StonedEdge/Retro-Lite-CM5/enclosure/Solidworks/AX210 PCIe Card.SLDASM

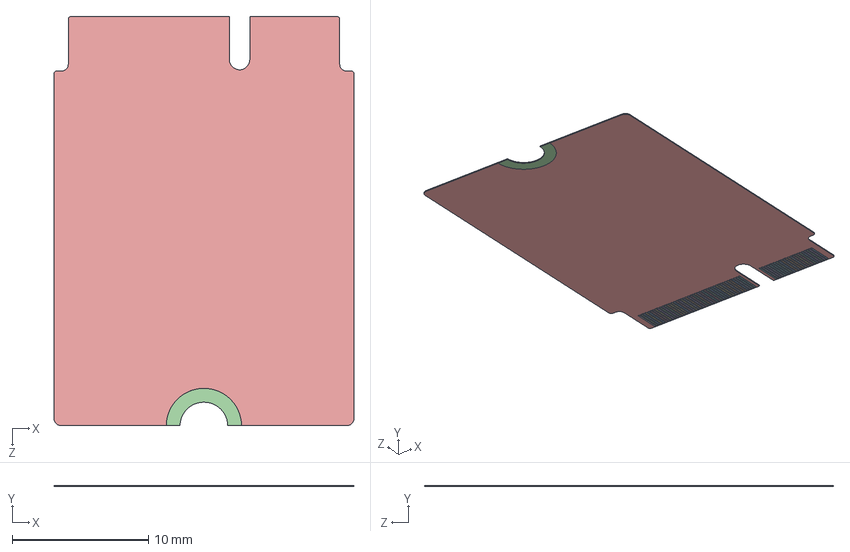
[picture p15: CAD file, 2024-07-26]
enclosure/Solidworks/AX210 PCIe Card.SLDASM
22.0 x 0.1 x 30.0 mm
AX210 PCIe Card-0
AX210 PCIe Card-1
AX210 PCIe Card-2
