StonedEdge/Retro-Lite-CM5/enclosure/Solidworks/Assembly Right PCB Controller.SLDASM

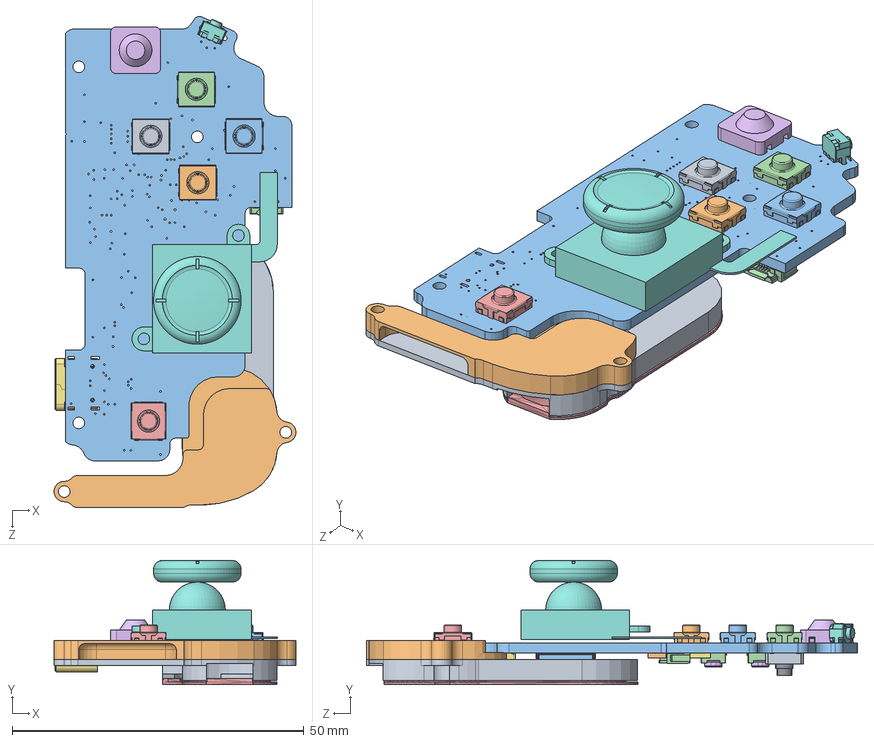
[picture p16: CAD file, 2024-07-26]
enclosure/Solidworks/Assembly Right PCB Controller.SLDASM
41.5 x 21.2 x 84.1 mm
Speaker Duct
Speaker Duct Lower
Board (39)
Frame x 2
Cover x 2
Stem x 2
Terminal x 8
Switch Joystick Blank
dualtact_BBStore v1
MPU-6050--3DModel-STEP-1 v1
5034801700 v1
505110-0592 v1
Printed-Speaker-Duct-Lid v1
Single Silicone Cap
RP2040_QFN_PACKAGE v1
436333033816 v1
Retro Lite CM5 (Latest)-11
Retro Lite CM5 (Latest)-12
Retro Lite CM5 (Latest)-13
Retro Lite CM5 (Latest)-14
Retro Lite CM5 (Latest)-15
Retro Lite CM5 (Latest)-16
Retro Lite CM5 (Latest)-17
