StonedEdge/Retro-Lite-CM5/enclosure/Solidworks/ZR Trigger_1.SLDPRT

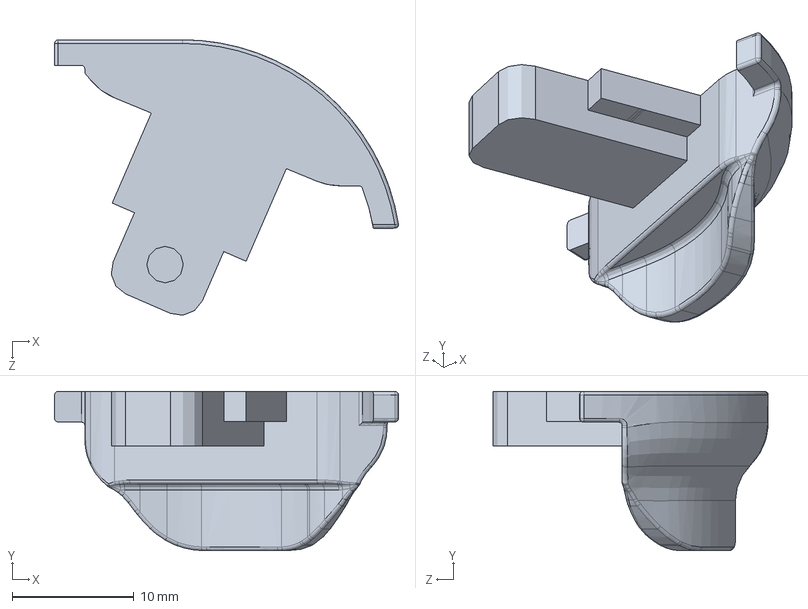
[picture p17: CAD file, 2024-07-26]
enclosure/Solidworks/ZR Trigger_1.SLDPRT
28.3 x 13.1 x 22.6 mm
