StonedEdge/Retro-Lite-CM5/enclosure/STL_V2/Case Front (OLED) - Fix outer surface face.stl

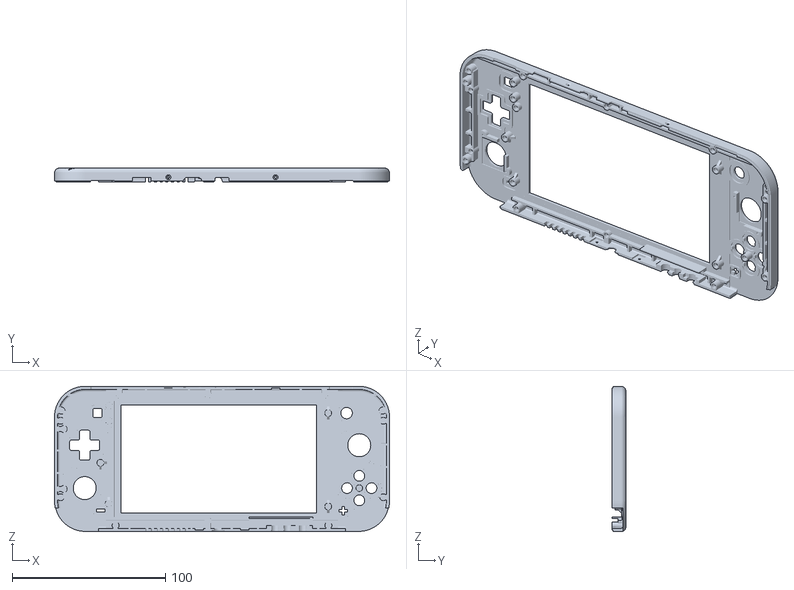
[picture p18: CAD file, 2025-11-29]
enclosure/STL_V2/Case Front (OLED) - Fix outer surface face.stl
218.8 x 9.00 x 95.0
