StonedEdge/Retro-Lite-CM5/enclosure/Solidworks/Start_Button_1.SLDPRT

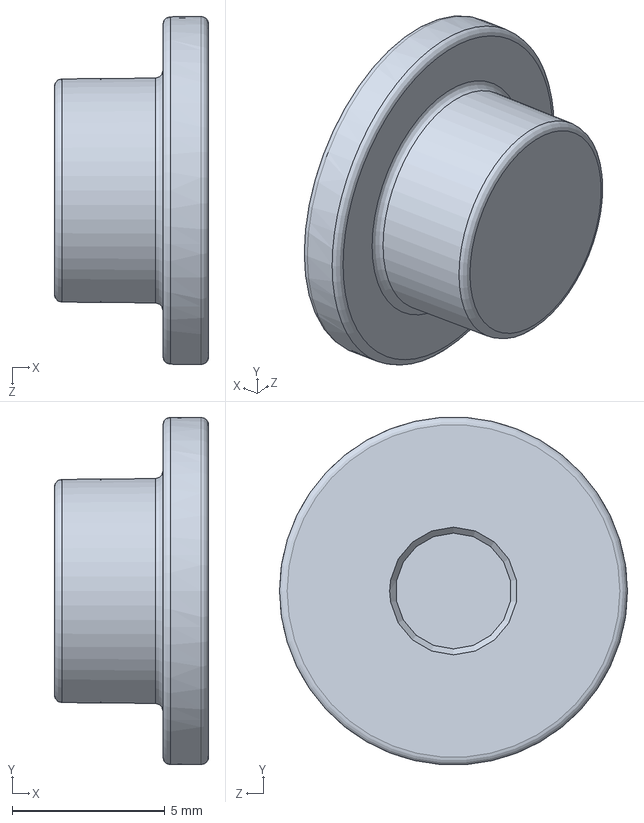
[picture p19: CAD file, 2024-07-26]
enclosure/Solidworks/Start_Button_1.SLDPRT
5.05 x 11.4 x 11.4 mm
