StonedEdge/Retro-Lite-CM5/enclosure/Solidworks/U9.SLDPRT

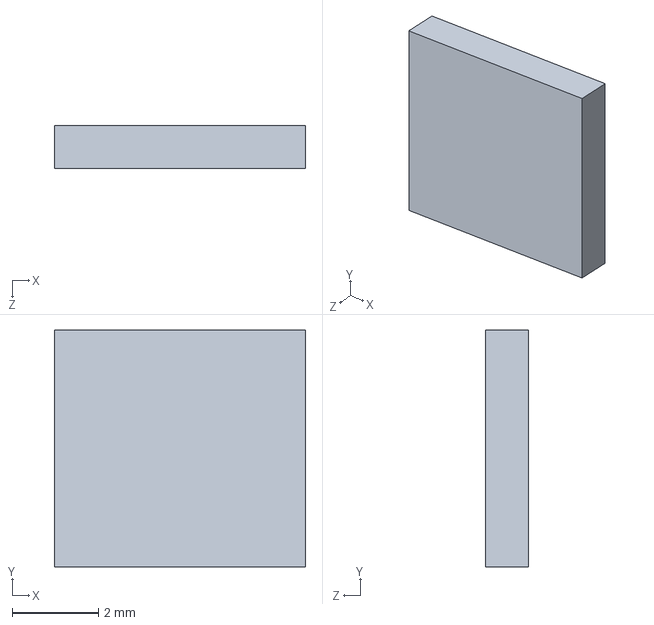
[picture p20: CAD file, 2024-07-26]
enclosure/Solidworks/U9.SLDPRT
5.84 x 5.50 x 1.00 mm
