StonedEdge/Retro-Lite-CM5/enclosure/Solidworks/Retro Lite CM5 (Latest)-18.SLDPRT

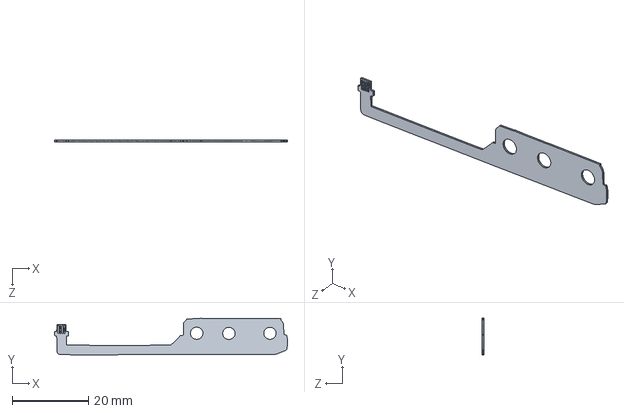
[picture p21: CAD file, 2024-07-26]
enclosure/Solidworks/Retro Lite CM5 (Latest)-18.SLDPRT
61.0 x 9.58 x 0.4 mm
