StonedEdge/Retro-Lite-CM5/enclosure/STL_V2/Button Spacers.stl

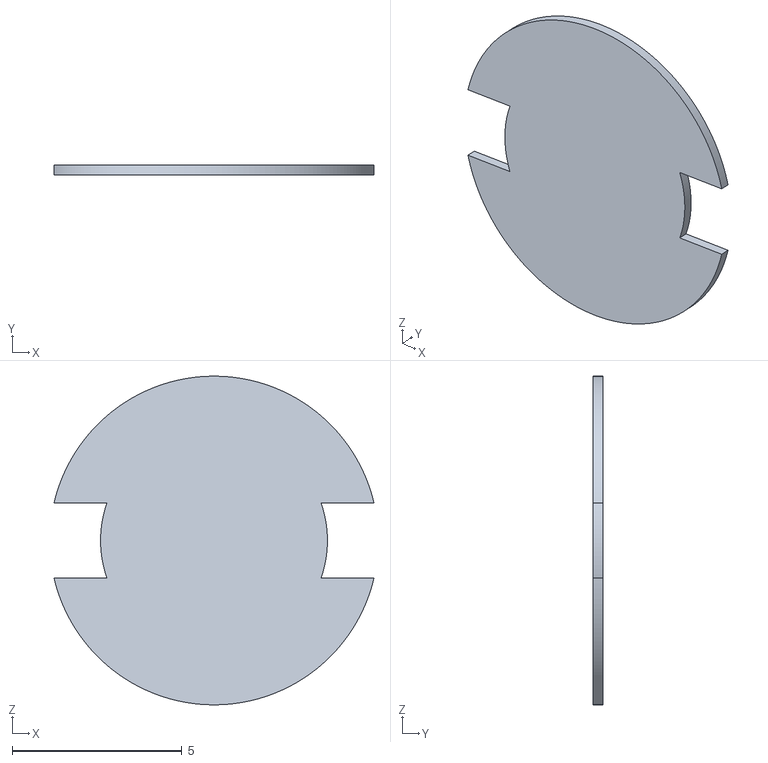
[picture p22: CAD file, 2025-06-07]
enclosure/STL_V2/Button Spacers.stl
9.43 x 0.3 x 9.69
