StonedEdge/Retro-Lite-CM5/enclosure/Solidworks/Retro Lite CM5 (Latest)-12.SLDPRT

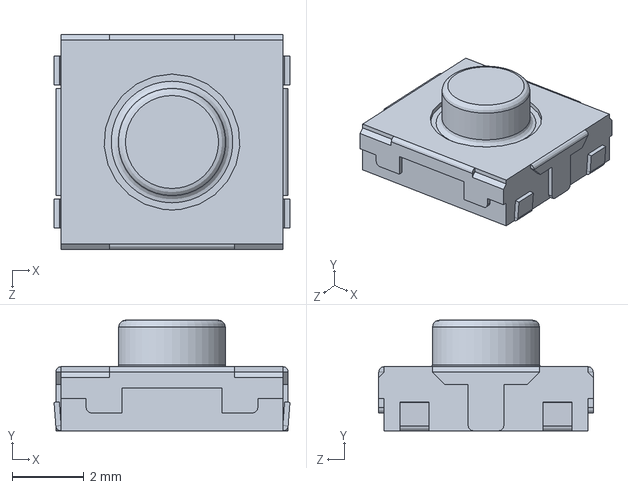
[picture p23: CAD file, 2024-07-26]
enclosure/Solidworks/Retro Lite CM5 (Latest)-12.SLDPRT
6.60 x 3.10 x 6.00 mm
