StonedEdge/Retro-Lite-CM5/enclosure/STL_V2/Button Rotation Stopper Bracket.stl

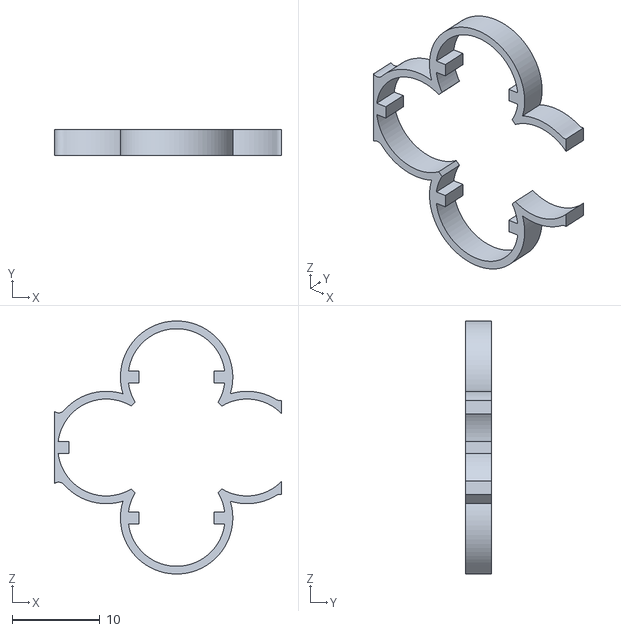
[picture p24: CAD file, 2025-06-07]
enclosure/STL_V2/Button Rotation Stopper Bracket.stl
25.9 x 3.00 x 28.8
