StonedEdge/Retro-Lite-CM5/enclosure/STL_V2/Battery Bracket (5000mAh).stl

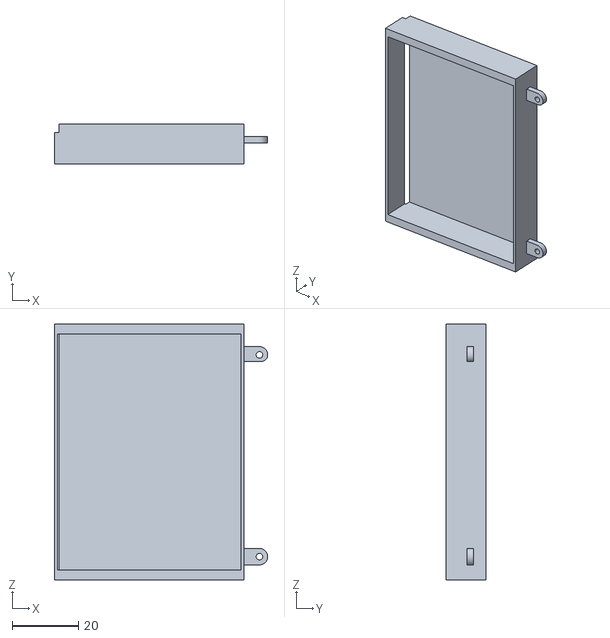
[picture p25: CAD file, 2025-06-03]
enclosure/STL_V2/Battery Bracket (5000mAh).stl
64.5 x 12.0 x 77.4
