StonedEdge/Retro-Lite-CM5/enclosure/Solidworks/Speaker Duct Lower.SLDPRT

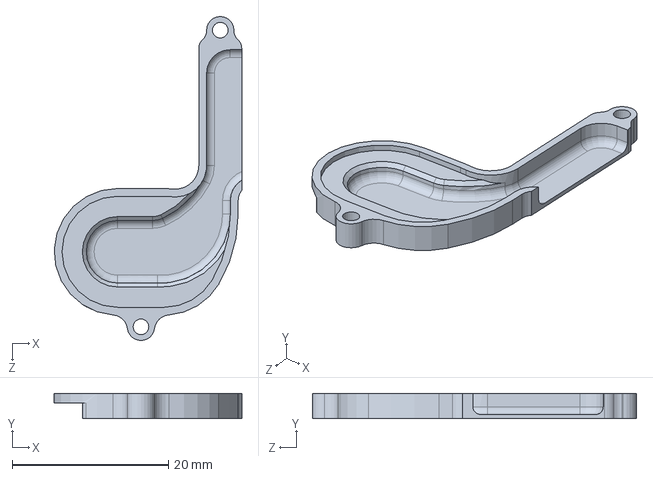
[picture p26: CAD file, 2024-07-26]
enclosure/Solidworks/Speaker Duct Lower.SLDPRT
24.0 x 3.20 x 41.5 mm
