StonedEdge/Retro-Lite-CM5/enclosure/STL_V2/Case Rear (Smaller Vent Holes).stl

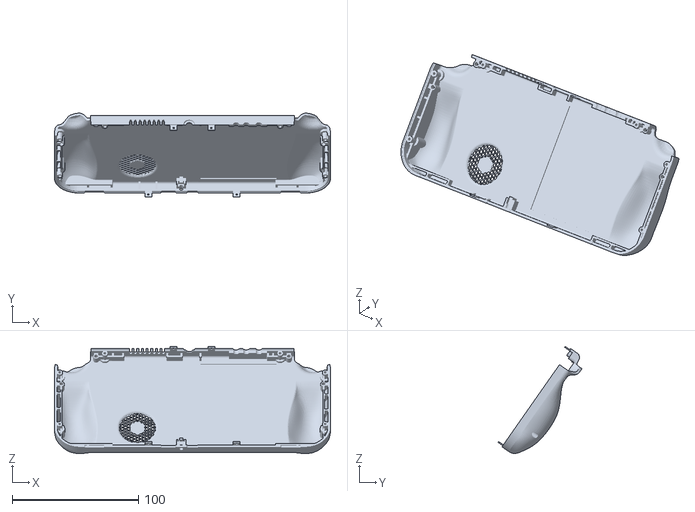
[picture p27: CAD file, 2024-12-22]
enclosure/STL_V2/Case Rear (Smaller Vent Holes).stl
219.0 x 66.5 x 84.9
