StonedEdge/Retro-Lite-CM5/enclosure/Solidworks/Terminal.SLDPRT

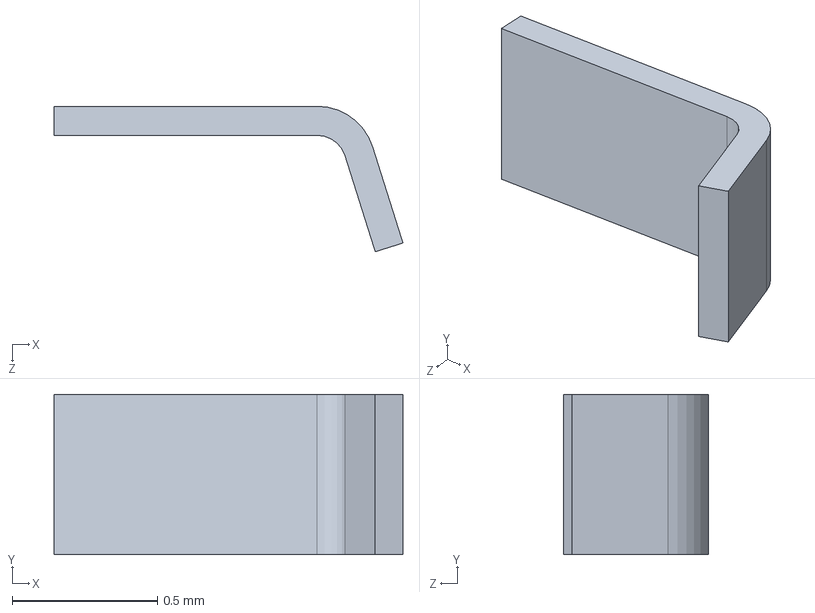
[picture p28: CAD file, 2024-07-26]
enclosure/Solidworks/Terminal.SLDPRT
1.20 x 0.55 x 0.5 mm
