StonedEdge/Retro-Lite-CM5/enclosure/STL_V2/Case Front (OLED).stl

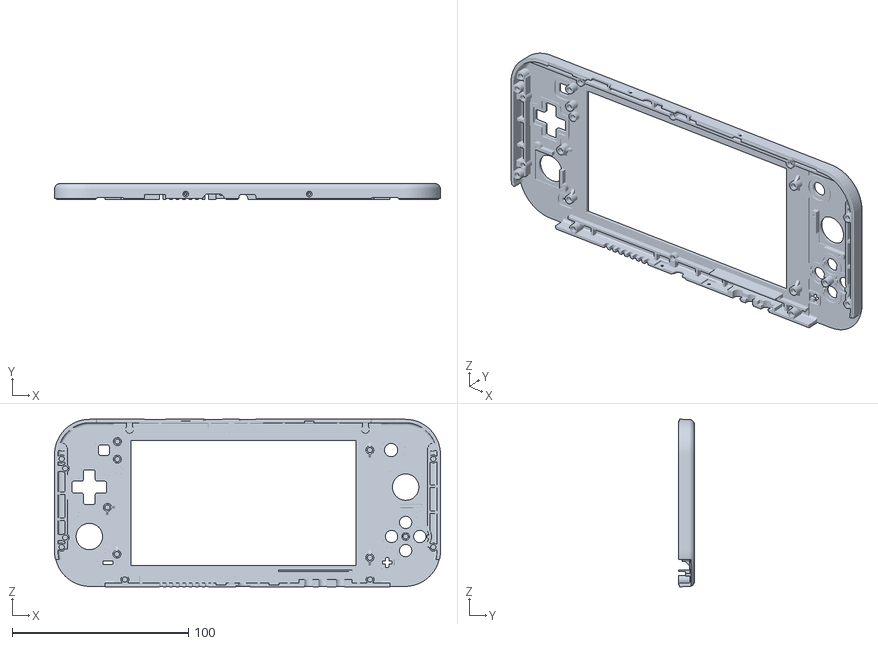
[picture p29: CAD file, 2024-09-26]
enclosure/STL_V2/Case Front (OLED).stl
218.8 x 9.00 x 95.0
