StonedEdge/Retro-Lite-CM5/enclosure/STL_V2/Battery Bracket (8000mAh).stl

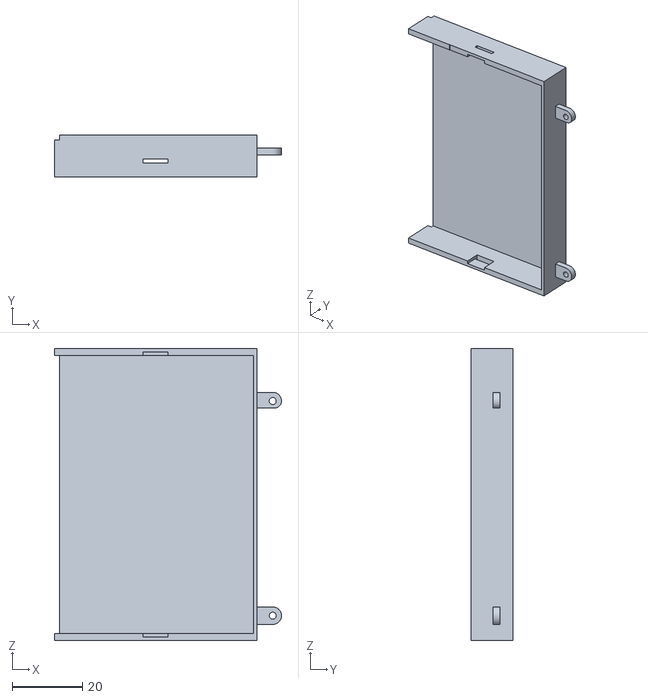
[picture p30: CAD file, 2024-07-11]
enclosure/STL_V2/Battery Bracket (8000mAh).stl
64.5 x 12.0 x 83.0
