StonedEdge/Retro-Lite-CM5/enclosure/Solidworks/Switch Joystick Blank.SLDPRT

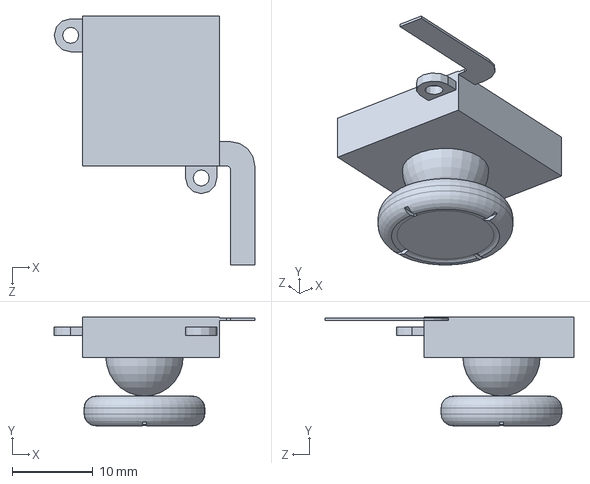
[picture p31: CAD file, 2024-07-26]
enclosure/Solidworks/Switch Joystick Blank.SLDPRT
24.9 x 13.5 x 30.9 mm
