StonedEdge/Retro-Lite-CM5/enclosure/STL_V2/Trigger_Spacer.stl

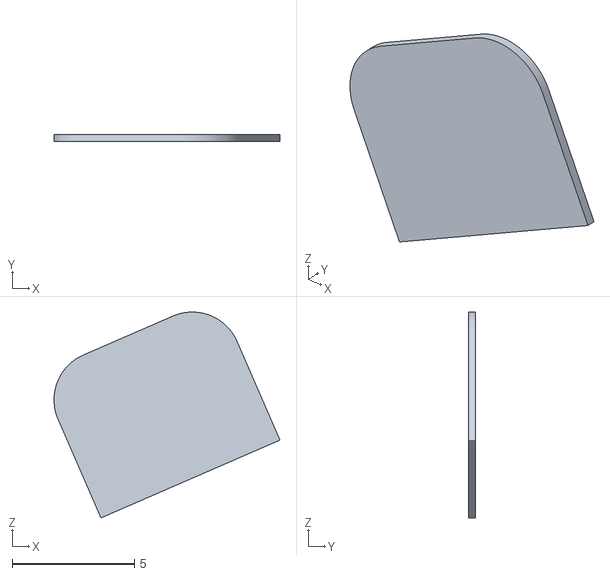
[picture p32: CAD file, 2024-07-11]
enclosure/STL_V2/Trigger_Spacer.stl
9.26 x 0.3 x 8.44
