StonedEdge/Retro-Lite-CM5/enclosure/Solidworks/Speaker Duct.SLDPRT

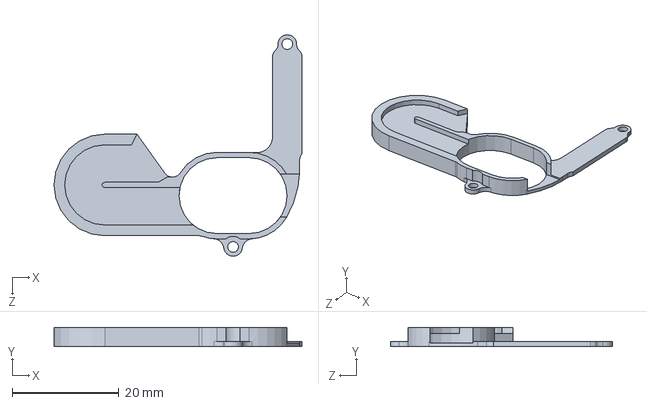
[picture p33: CAD file, 2024-07-26]
enclosure/Solidworks/Speaker Duct.SLDPRT
46.4 x 3.60 x 41.5 mm
