StonedEdge/Retro-Lite-CM5/enclosure/STL_V2/Power Button.stl

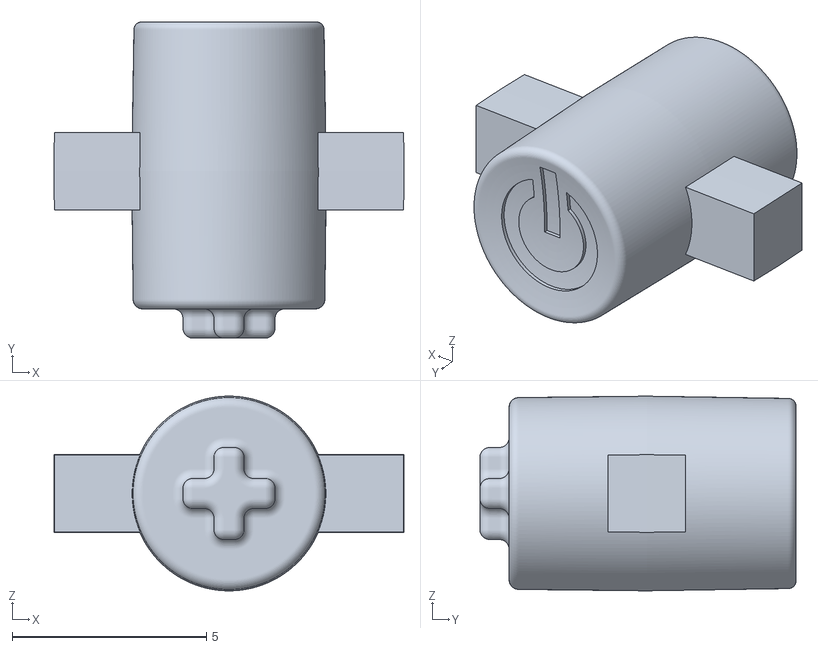
[picture p34: CAD file, 2024-06-27]
enclosure/STL_V2/Power Button.stl
9.02 x 8.15 x 5.02
