StonedEdge/Retro-Lite-CM5/enclosure/Solidworks/VLCF4020T-220MR56--3DModel-STEP-56544 v1.SLDPRT

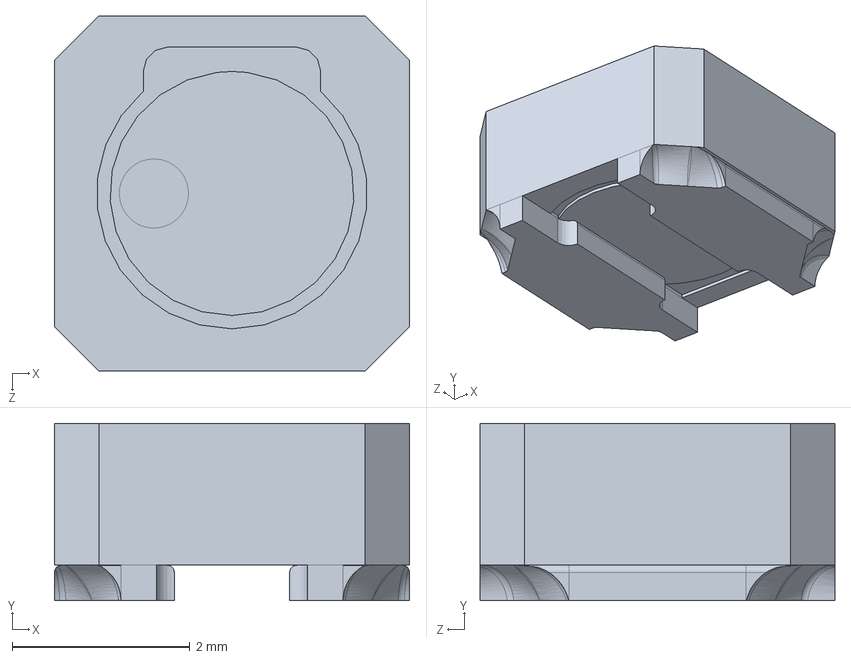
[picture p35: CAD file, 2024-07-26]
enclosure/Solidworks/VLCF4020T-220MR56--3DModel-STEP-56544 v1.SLDPRT
4.00 x 2.00 x 4.00 mm
