StonedEdge/Retro-Lite-CM5/enclosure/STL_V2/Case Rear.stl

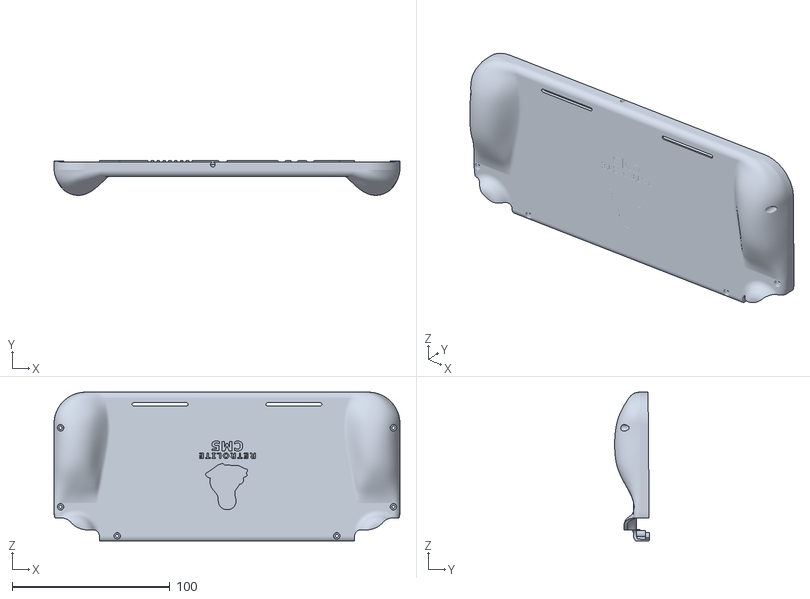
[picture p36: CAD file, 2024-06-27]
enclosure/STL_V2/Case Rear.stl
219.0 x 22.0 x 94.1
