StonedEdge/Retro-Lite-CM5/enclosure/Solidworks/NuckDeck B_1.SLDPRT

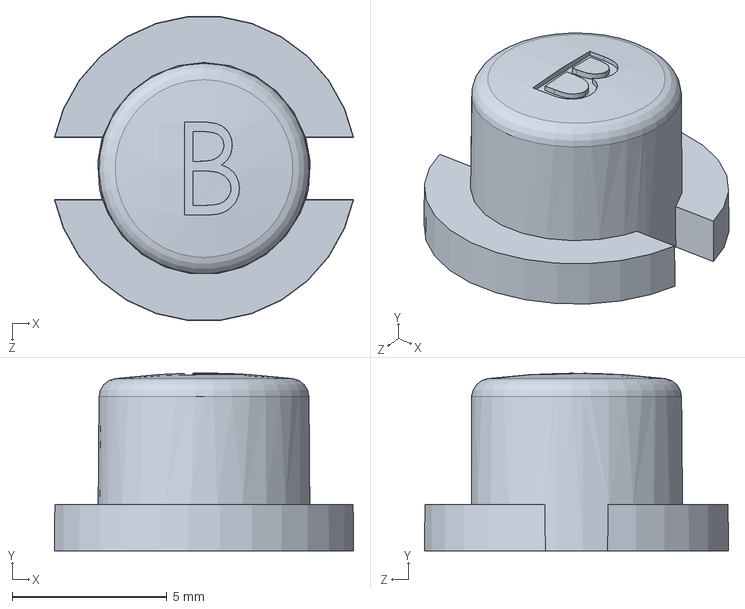
[picture p37: CAD file, 2024-07-26]
enclosure/Solidworks/NuckDeck B_1.SLDPRT
9.68 x 5.75 x 9.83 mm
