StonedEdge/Retro-Lite-CM5/enclosure/STL_V2/Volume Buttons.stl

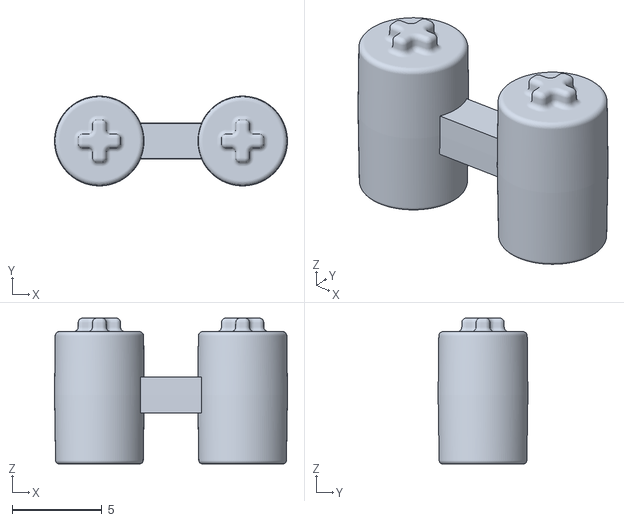
[picture p38: CAD file, 2024-06-27]
enclosure/STL_V2/Volume Buttons.stl
13.0 x 5.02 x 8.15
