StonedEdge/Retro-Lite-CM5/enclosure/STL_V2/Case Front.stl

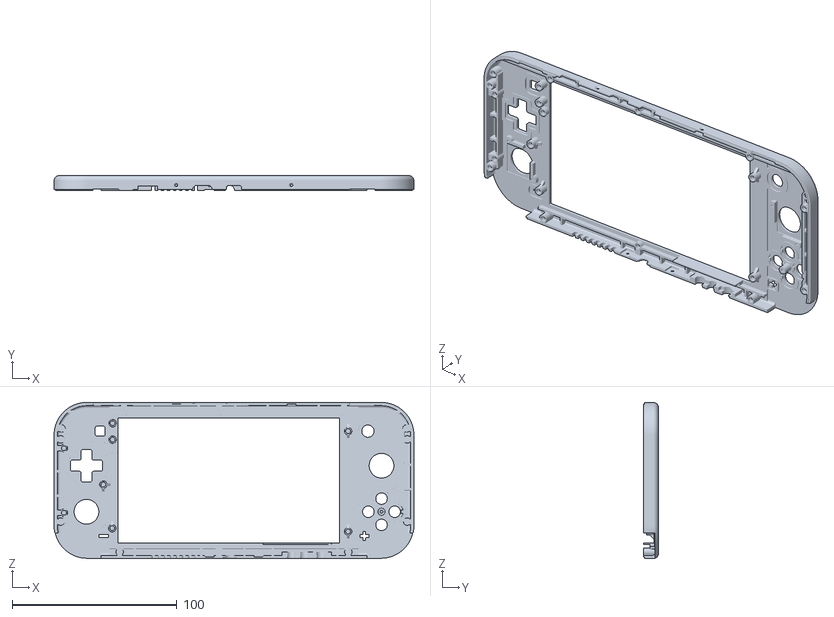
[picture p39: CAD file, 2024-06-27]
enclosure/STL_V2/Case Front.stl
218.8 x 9.00 x 95.0
