StonedEdge/Retro-Lite-CM5/enclosure/Solidworks/TSIC 306 SOP-8--3DModel-STEP-510211 v1.SLDPRT

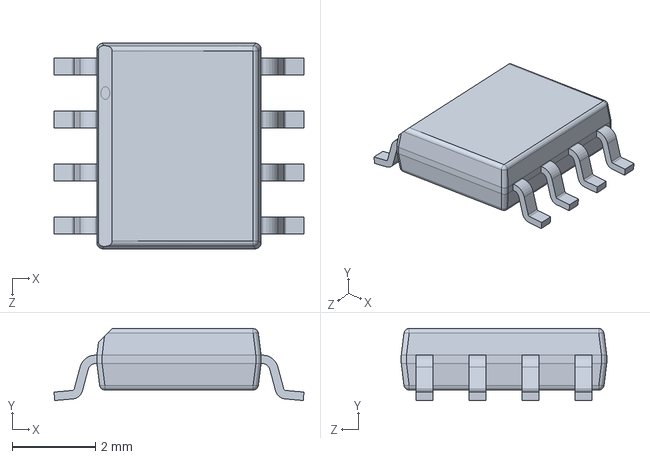
[picture p40: CAD file, 2024-07-26]
enclosure/Solidworks/TSIC 306 SOP-8--3DModel-STEP-510211 v1.SLDPRT
5.99 x 1.73 x 4.93 mm
