StonedEdge/Retro-Lite-CM5/enclosure/STL_V2/Fan Bracket.stl

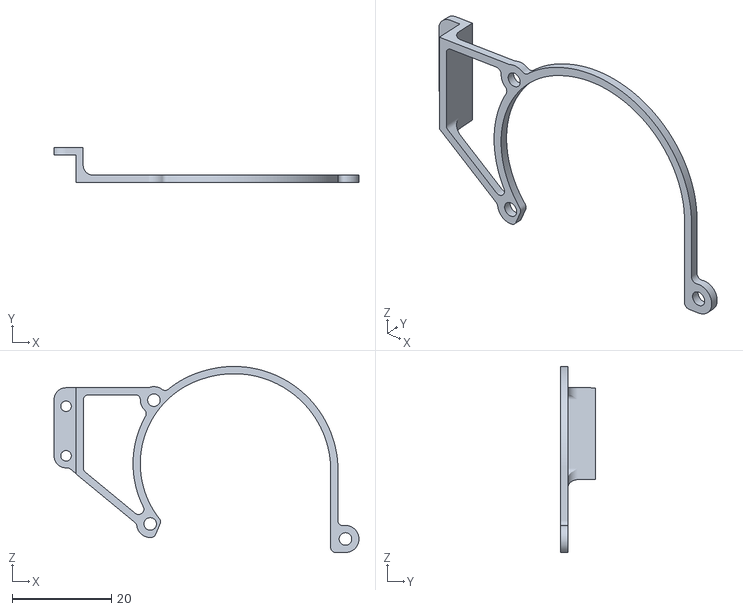
[picture p41: CAD file, 2024-06-27]
enclosure/STL_V2/Fan Bracket.stl
61.5 x 7.08 x 37.5
