StonedEdge/Retro-Lite-CM5/enclosure/Solidworks/refine_Cut001.SLDPRT

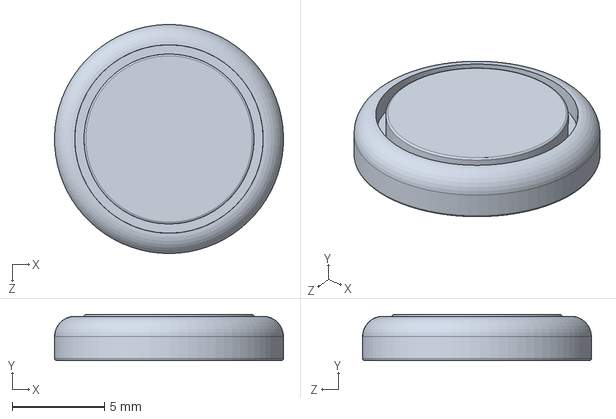
[picture p42: CAD file, 2024-07-26]
enclosure/Solidworks/refine_Cut001.SLDPRT
12.4 x 2.50 x 12.4 mm
