StonedEdge/Retro-Lite-CM5/enclosure/STL_V2/Rear Trigger Bracket .stl

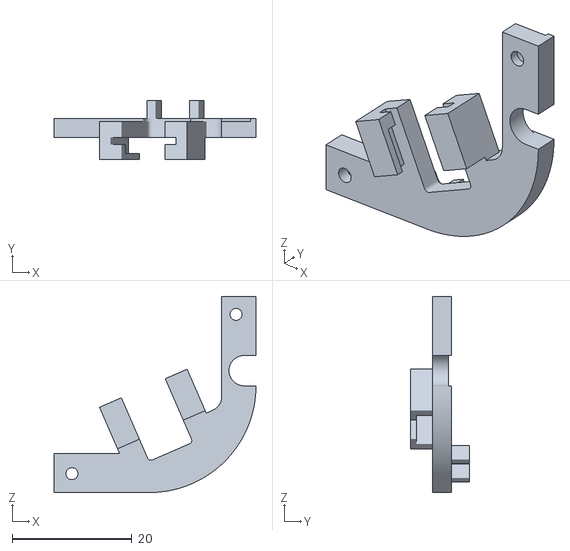
[picture p43: CAD file, 2024-06-08]
enclosure/STL_V2/Rear Trigger Bracket .stl
33.8 x 9.90 x 32.8
