StonedEdge/Retro-Lite-CM5/enclosure/Solidworks/U4302.SLDPRT

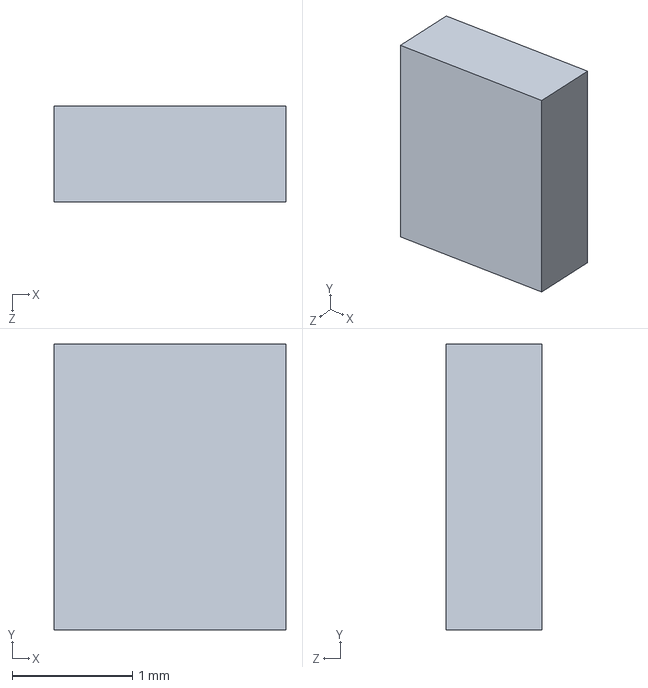
[picture p44: CAD file, 2024-07-26]
enclosure/Solidworks/U4302.SLDPRT
1.93 x 2.38 x 0.8 mm
