StonedEdge/Retro-Lite-CM5/enclosure/Solidworks/Silicone Button Cap_DPAD.SLDPRT

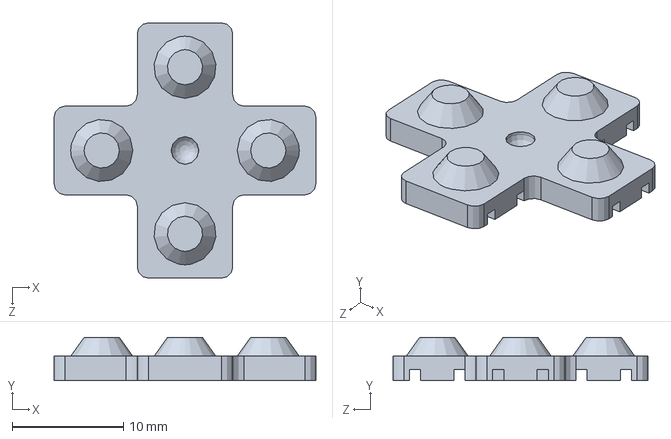
[picture p45: CAD file, 2024-07-26]
enclosure/Solidworks/Silicone Button Cap_DPAD.SLDPRT
23.6 x 3.90 x 23.0 mm
