StonedEdge/Retro-Lite-CM5/enclosure/STL_V2/Silicone_Membrane_Mold_Lower.stl

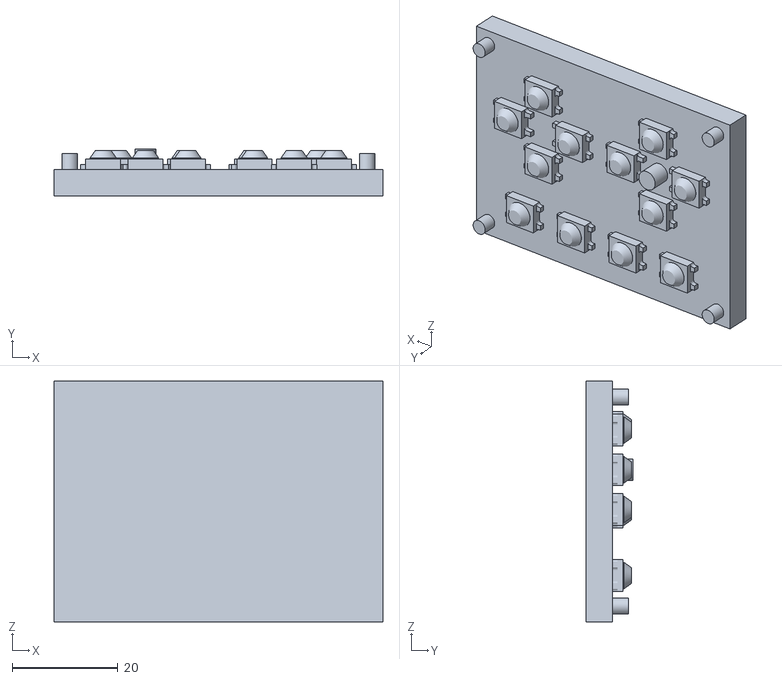
[picture p46: CAD file, 2024-04-26]
enclosure/STL_V2/Silicone_Membrane_Mold_Lower.stl
62.2 x 8.90 x 45.5
