StonedEdge/Retro-Lite-CM5/enclosure/Solidworks/refine_Revolution001.SLDPRT

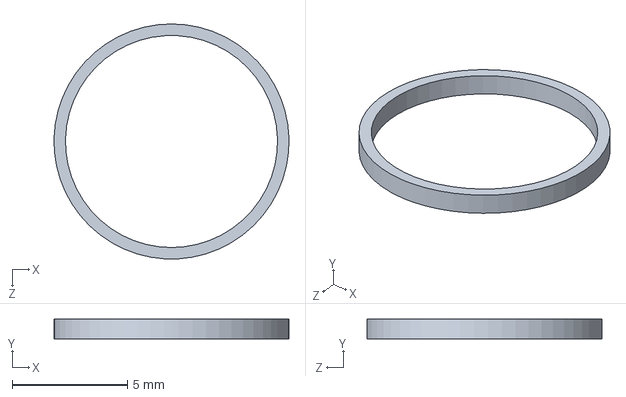
[picture p47: CAD file, 2024-07-26]
enclosure/Solidworks/refine_Revolution001.SLDPRT
10.2 x 0.85 x 10.2 mm
