StonedEdge/Retro-Lite-CM5/enclosure/STL_V2/Silicone_Membrane_Mold_Upper.stl

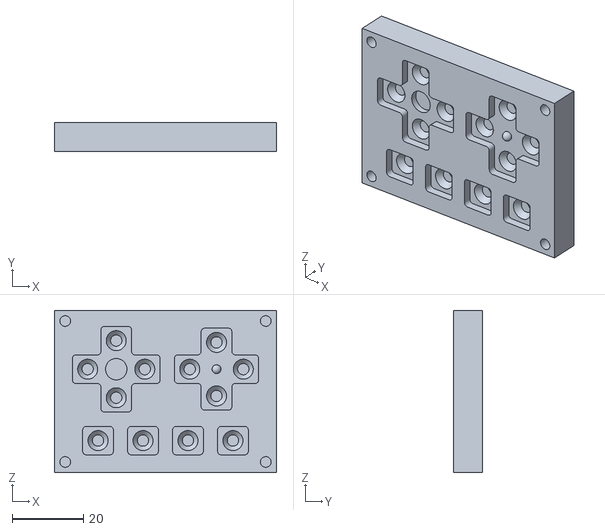
[picture p48: CAD file, 2024-04-26]
enclosure/STL_V2/Silicone_Membrane_Mold_Upper.stl
62.2 x 8.00 x 45.5
