StonedEdge/Retro-Lite-CM5/enclosure/Solidworks/Switch Lite Fan_1.SLDPRT

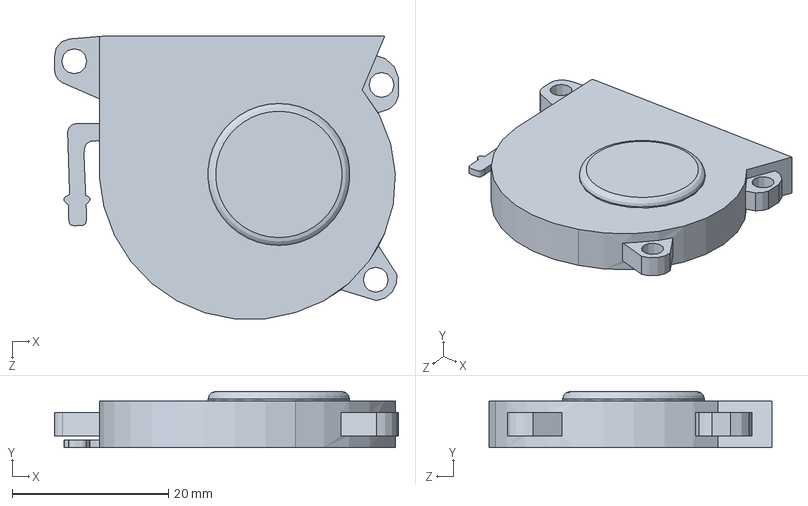
[picture p49: CAD file, 2024-07-26]
enclosure/Solidworks/Switch Lite Fan_1.SLDPRT
44.1 x 7.20 x 36.3 mm
