StonedEdge/Retro-Lite-CM5/enclosure/Solidworks/Y1.SLDPRT

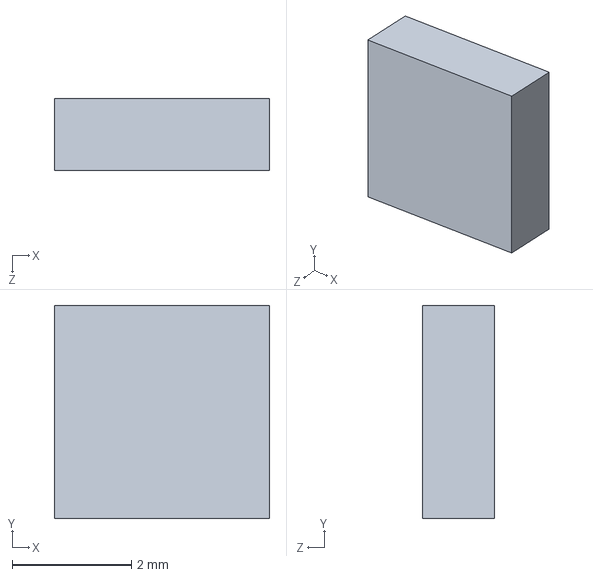
[picture p50: CAD file, 2024-07-26]
enclosure/Solidworks/Y1.SLDPRT
3.60 x 3.57 x 1.20 mm
