StonedEdge/Retro-Lite-CM5/enclosure/Solidworks/U8.SLDPRT

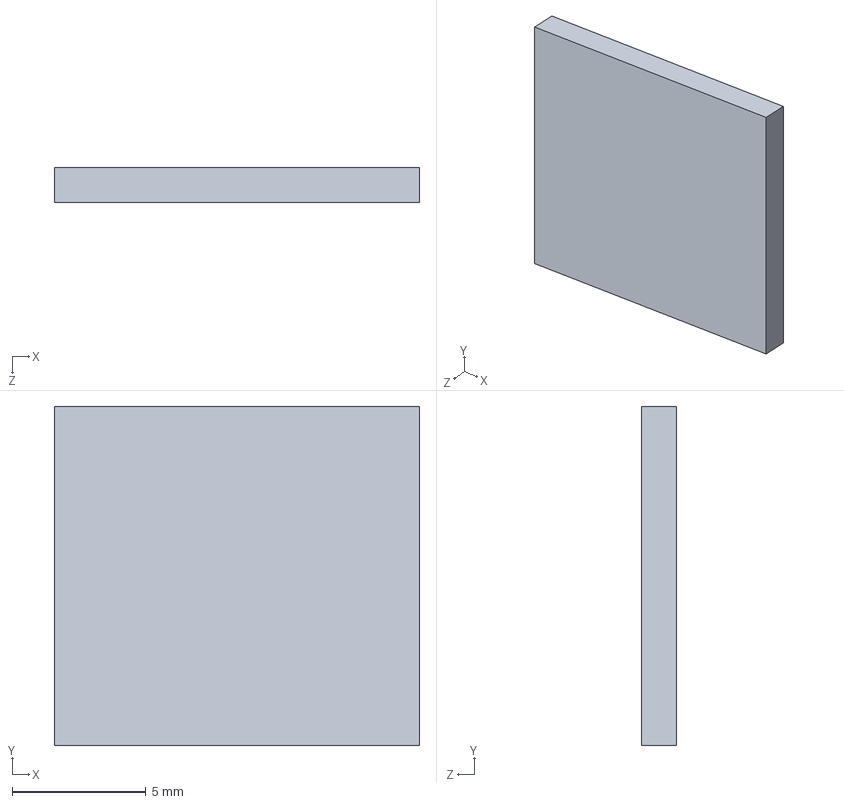
[picture p51: CAD file, 2024-07-26]
enclosure/Solidworks/U8.SLDPRT
13.7 x 12.7 x 1.30 mm
