StonedEdge/Retro-Lite-CM5/enclosure/Solidworks/U4301.SLDPRT

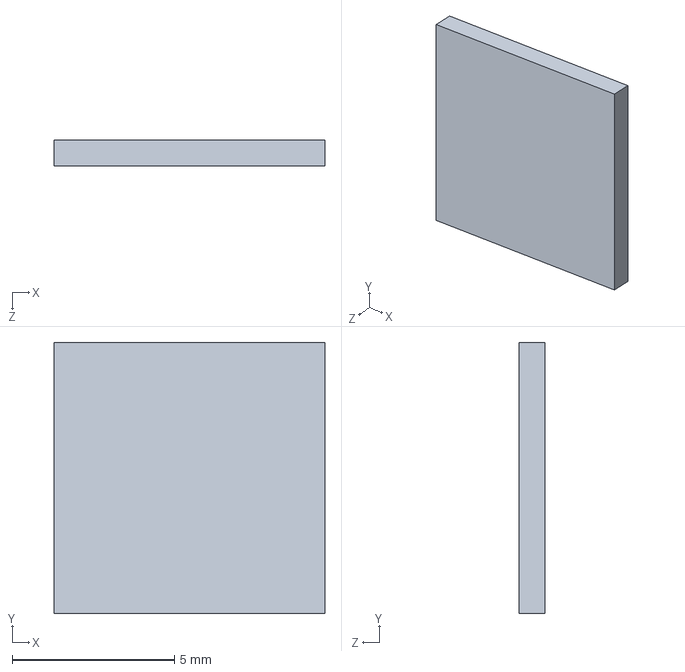
[picture p52: CAD file, 2024-07-26]
enclosure/Solidworks/U4301.SLDPRT
8.35 x 8.35 x 0.8 mm
