StonedEdge/Retro-Lite-CM5/enclosure/STL_V2/Right Speaker Cover.stl

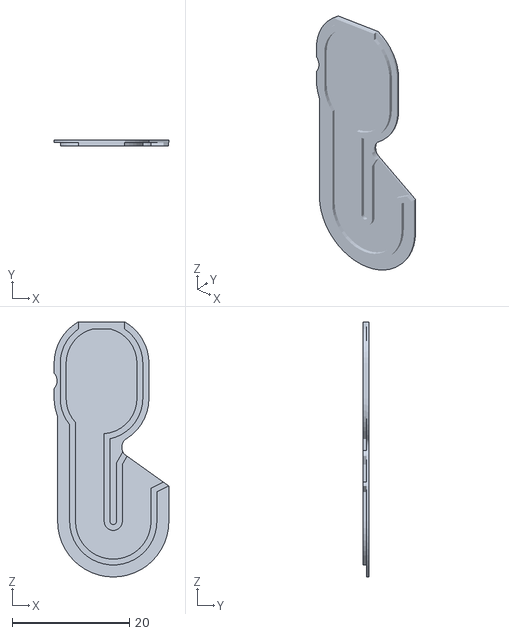
[picture p53: CAD file, 2024-03-31]
enclosure/STL_V2/Right Speaker Cover.stl
19.6 x 1.00 x 43.5
