StonedEdge/Retro-Lite-CM5/enclosure/Solidworks/R24.SLDPRT

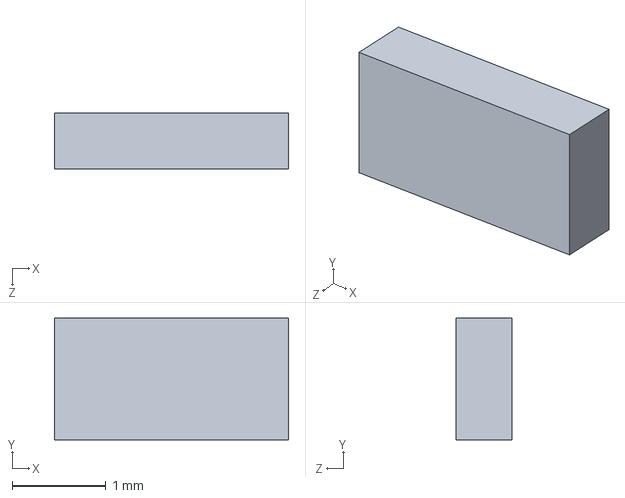
[picture p54: CAD file, 2024-07-26]
enclosure/Solidworks/R24.SLDPRT
2.50 x 1.30 x 0.6 mm
