StonedEdge/Retro-Lite-CM5/enclosure/Solidworks/Silicone Button Cap_Circle.SLDPRT

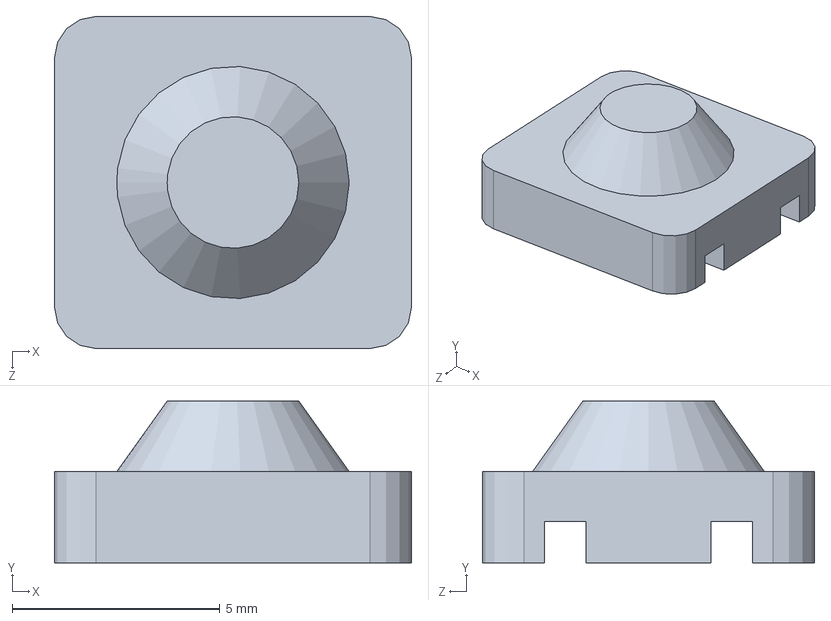
[picture p55: CAD file, 2024-07-26]
enclosure/Solidworks/Silicone Button Cap_Circle.SLDPRT
8.60 x 3.90 x 8.00 mm
