StonedEdge/Retro-Lite-CM5/enclosure/Solidworks/Q4.SLDPRT

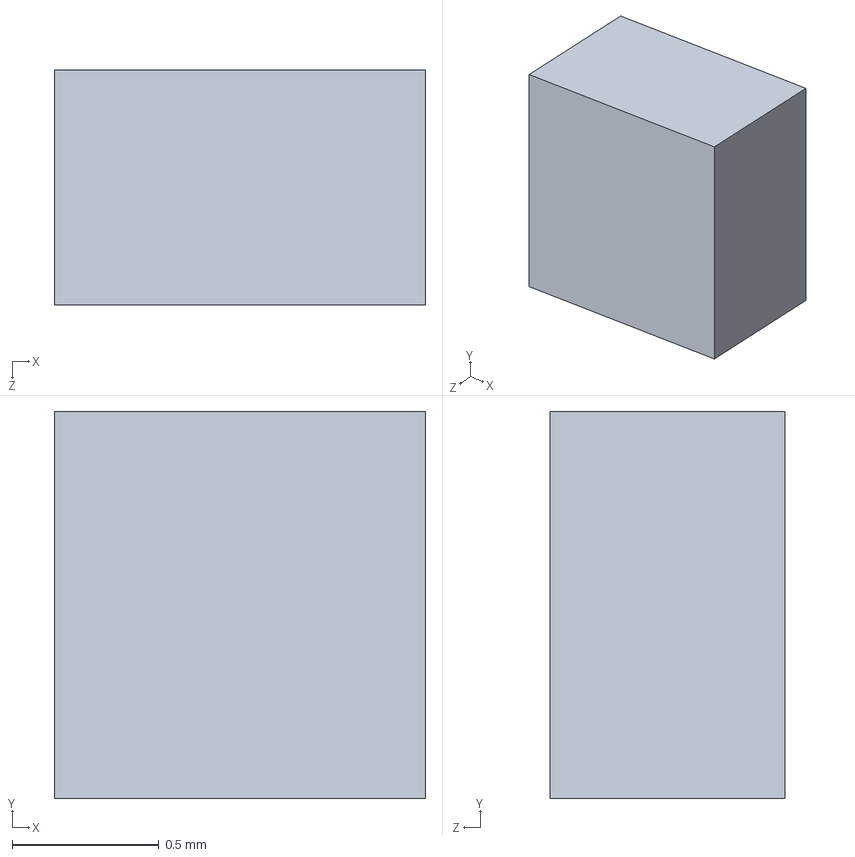
[picture p56: CAD file, 2024-07-26]
enclosure/Solidworks/Q4.SLDPRT
1.27 x 1.32 x 0.8 mm
