StonedEdge/Retro-Lite-CM5/enclosure/STL_V2/Plus Hotkey.stl

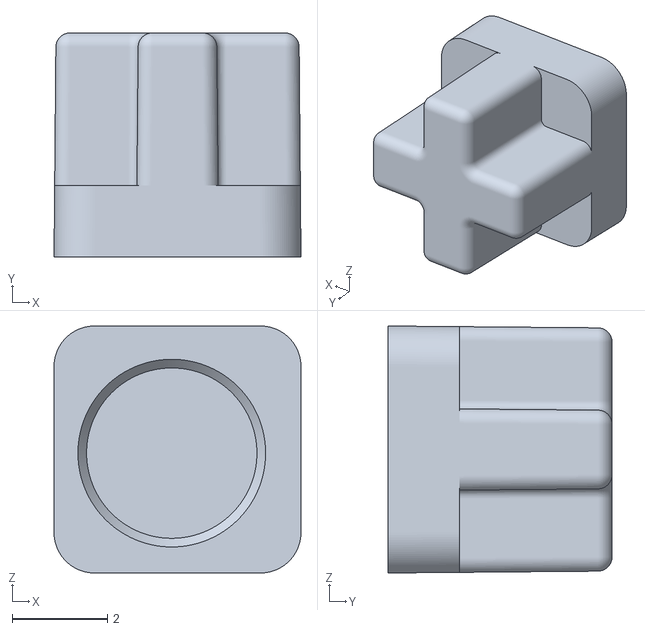
[picture p57: CAD file, 2024-03-04]
enclosure/STL_V2/Plus Hotkey.stl
5.18 x 4.70 x 5.18
