StonedEdge/Retro-Lite-CM5/enclosure/STL_V2/Trigger.stl

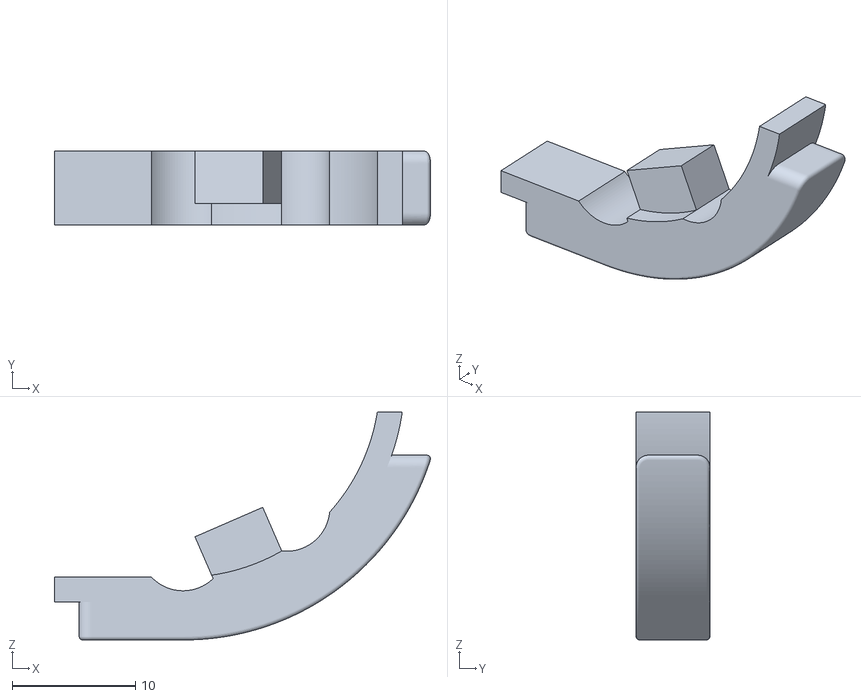
[picture p58: CAD file, 2024-02-13]
enclosure/STL_V2/Trigger.stl
30.5 x 6.00 x 18.5
