StonedEdge/Retro-Lite-CM5/enclosure/Solidworks/Stem.SLDPRT

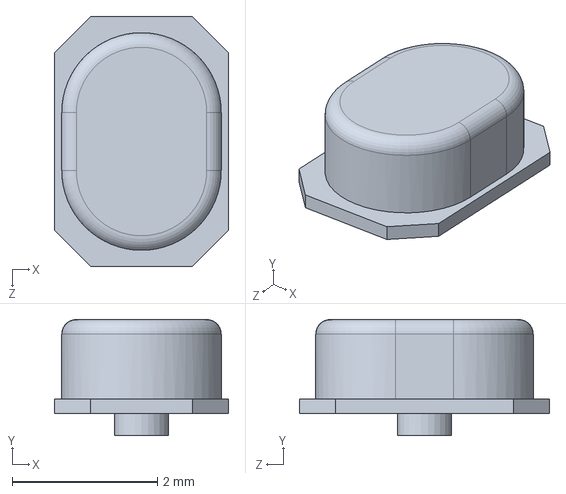
[picture p59: CAD file, 2024-07-26]
enclosure/Solidworks/Stem.SLDPRT
2.40 x 1.60 x 3.45 mm
