StonedEdge/Retro-Lite-CM5/enclosure/Solidworks/Silicone Button Cap_ABXY.SLDPRT

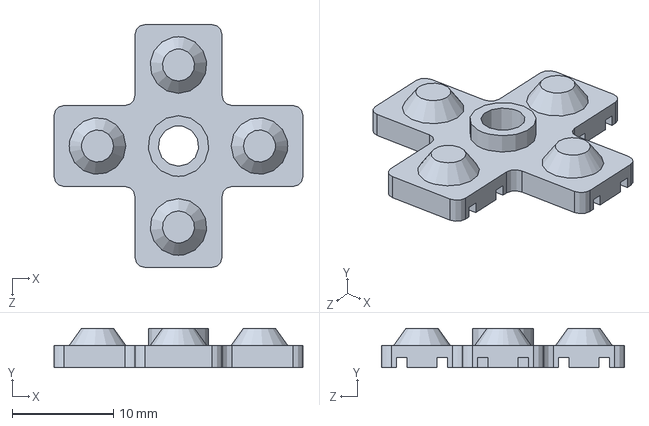
[picture p60: CAD file, 2024-07-26]
enclosure/Solidworks/Silicone Button Cap_ABXY.SLDPRT
24.6 x 3.90 x 24.0 mm
