StonedEdge/Retro-Lite-CM5/enclosure/STL_V2/B.stl

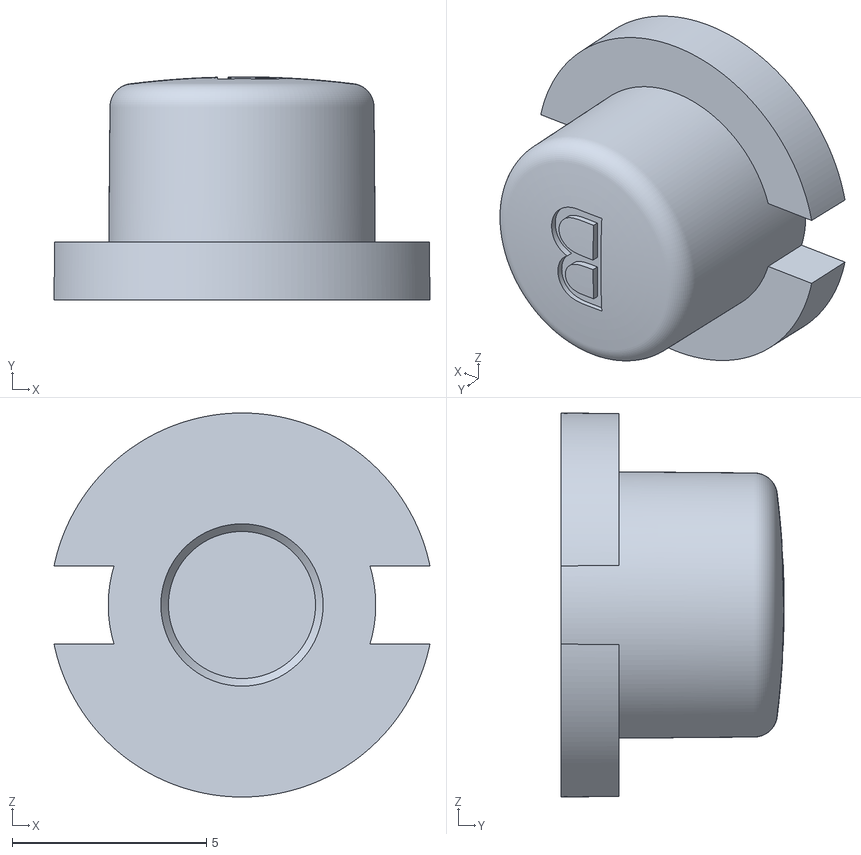
[picture p61: CAD file, 2024-02-08]
enclosure/STL_V2/B.stl
9.68 x 5.75 x 9.89
