StonedEdge/Retro-Lite-CM5/enclosure/STL_V2/Start.stl

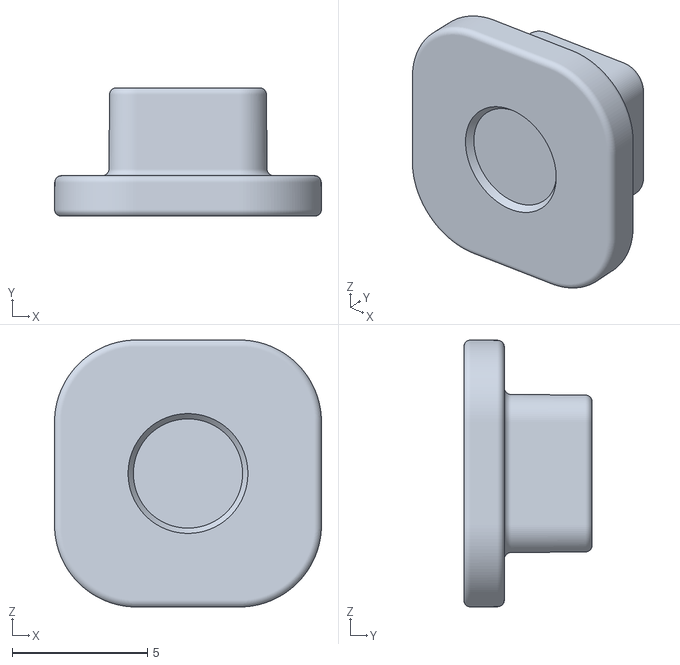
[picture p62: CAD file, 2024-02-08]
enclosure/STL_V2/Start.stl
9.88 x 4.75 x 9.88
