StonedEdge/Retro-Lite-CM5/enclosure/Solidworks/Retro Lite CM5 (Latest)-17.SLDPRT

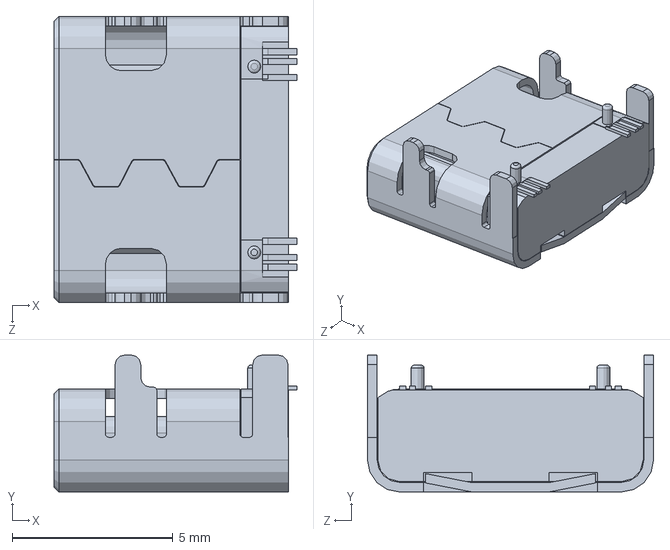
[picture p63: CAD file, 2024-07-26]
enclosure/Solidworks/Retro Lite CM5 (Latest)-17.SLDPRT
7.56 x 4.26 x 8.90 mm
