StonedEdge/Retro-Lite-CM5/enclosure/STL_V2/DPAD.stl

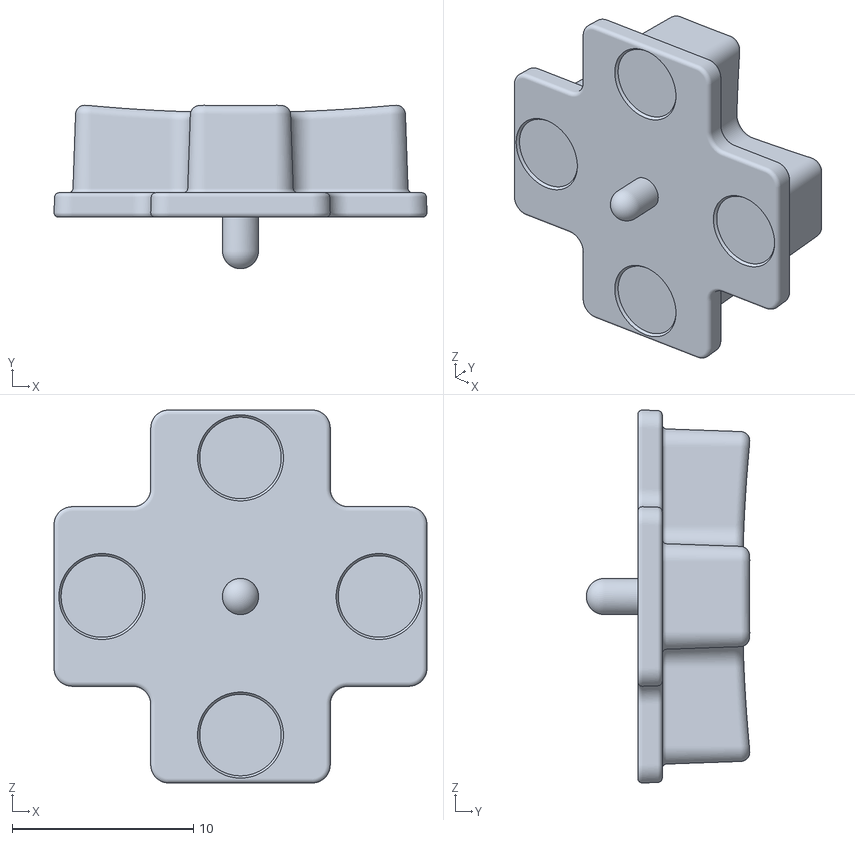
[picture p64: CAD file, 2024-02-08]
enclosure/STL_V2/DPAD.stl
20.6 x 9.03 x 20.6
