StonedEdge/Retro-Lite-CM5/enclosure/STL_V2/Minus Hotkey.stl

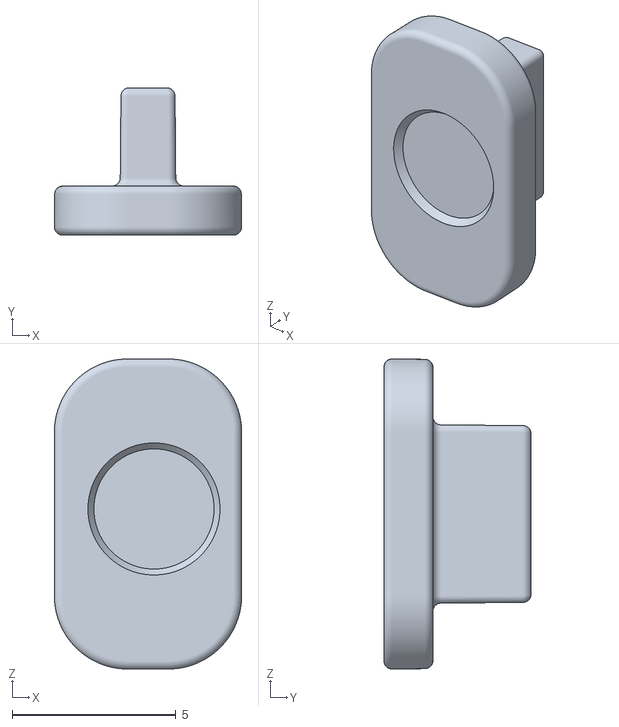
[picture p65: CAD file, 2024-02-08]
enclosure/STL_V2/Minus Hotkey.stl
5.72 x 4.50 x 9.47
