StonedEdge/Retro-Lite-CM5/enclosure/Solidworks/R1.SLDPRT

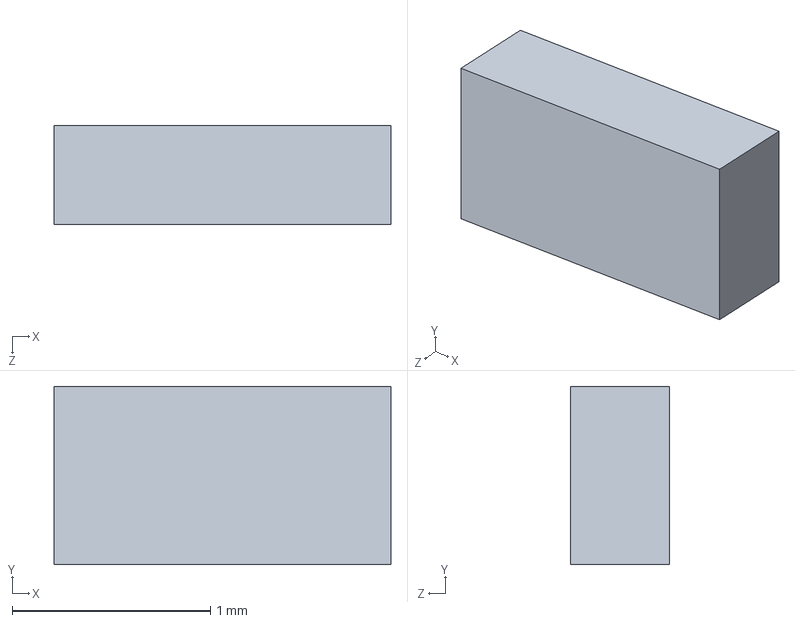
[picture p66: CAD file, 2024-07-26]
enclosure/Solidworks/R1.SLDPRT
1.70 x 0.9 x 0.5 mm
