StonedEdge/Retro-Lite-CM5/enclosure/Solidworks/U5.SLDPRT

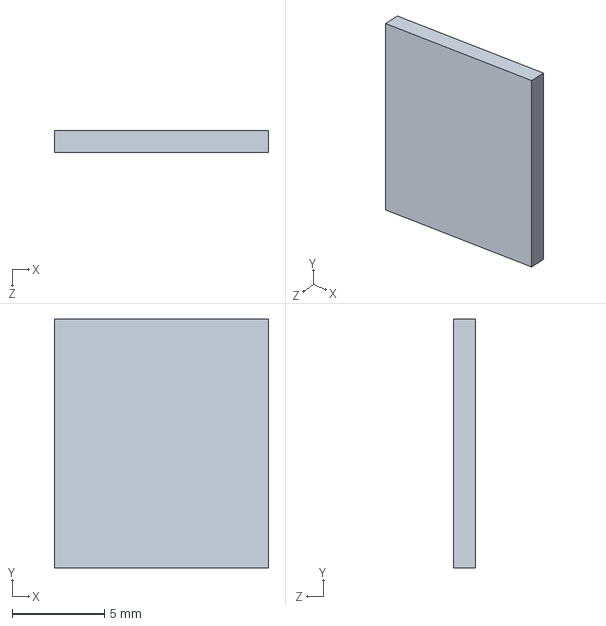
[picture p67: CAD file, 2024-07-26]
enclosure/Solidworks/U5.SLDPRT
11.6 x 13.5 x 1.20 mm
