StonedEdge/Retro-Lite-CM5/enclosure/Solidworks/Pin1.SLDPRT

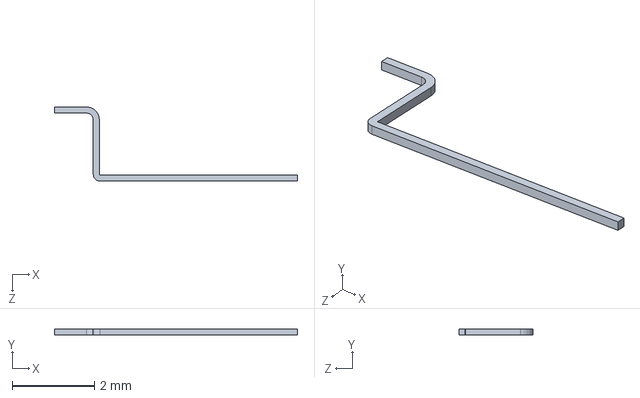
[picture p68: CAD file, 2024-07-26]
enclosure/Solidworks/Pin1.SLDPRT
5.90 x 0.15 x 1.80 mm
