StonedEdge/Retro-Lite-CM5/enclosure/Solidworks/U1.SLDPRT

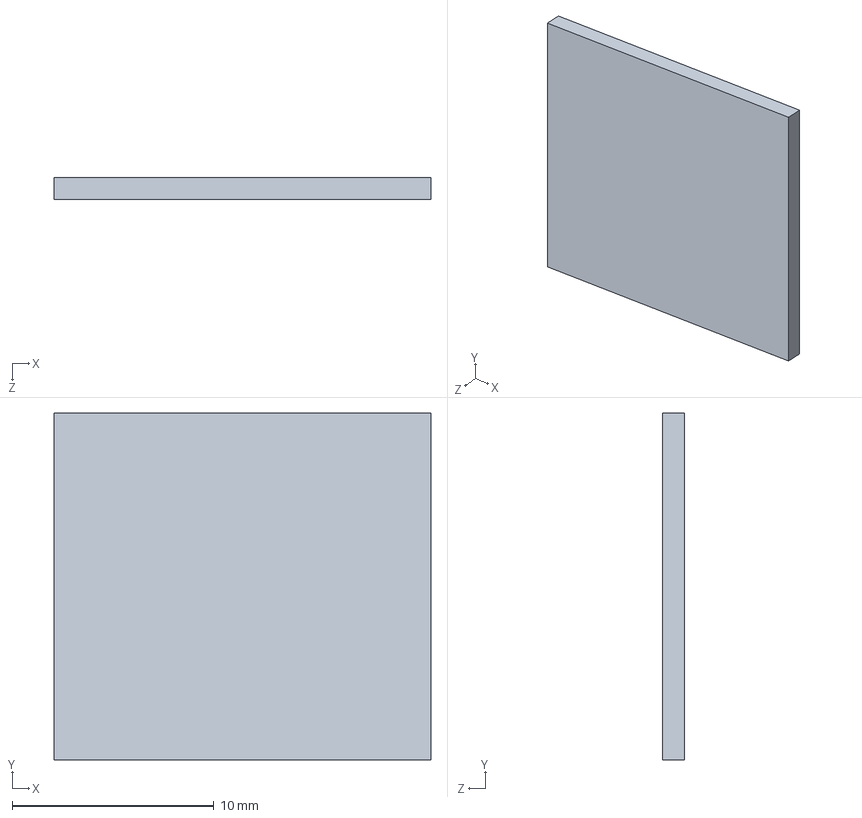
[picture p69: CAD file, 2024-07-26]
enclosure/Solidworks/U1.SLDPRT
18.7 x 17.2 x 1.10 mm
