StonedEdge/Retro-Lite-CM5/enclosure/Solidworks/Q5.SLDPRT

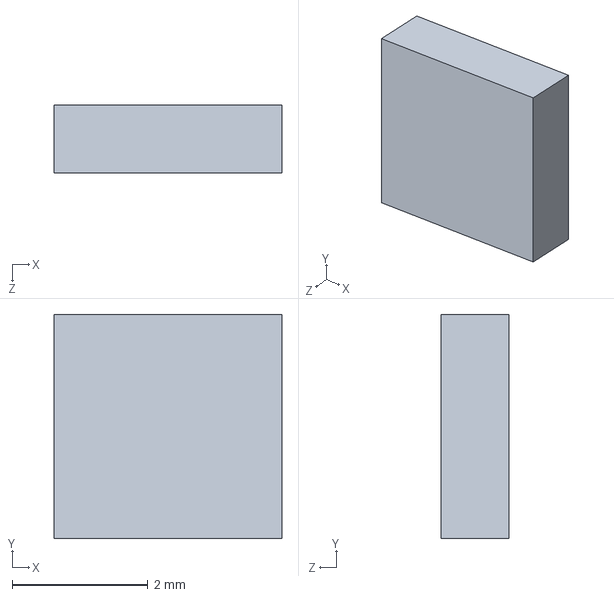
[picture p70: CAD file, 2024-07-26]
enclosure/Solidworks/Q5.SLDPRT
3.35 x 3.30 x 1.00 mm
