StonedEdge/Retro-Lite-CM5/enclosure/Solidworks/TPD4E05U06DQAR--3DModel-STEP-56544 v1.SLDPRT

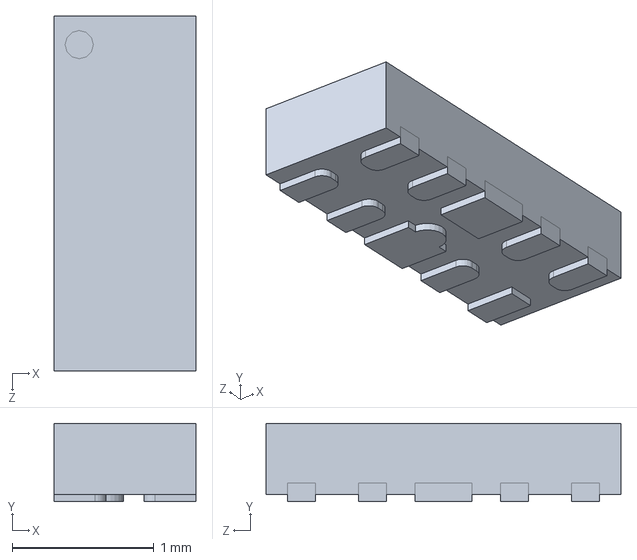
[picture p71: CAD file, 2024-07-26]
enclosure/Solidworks/TPD4E05U06DQAR--3DModel-STEP-56544 v1.SLDPRT
1.00 x 0.55 x 2.50 mm
