StonedEdge/Retro-Lite-CM5/enclosure/Solidworks/VLP-350-F.SLDPRT

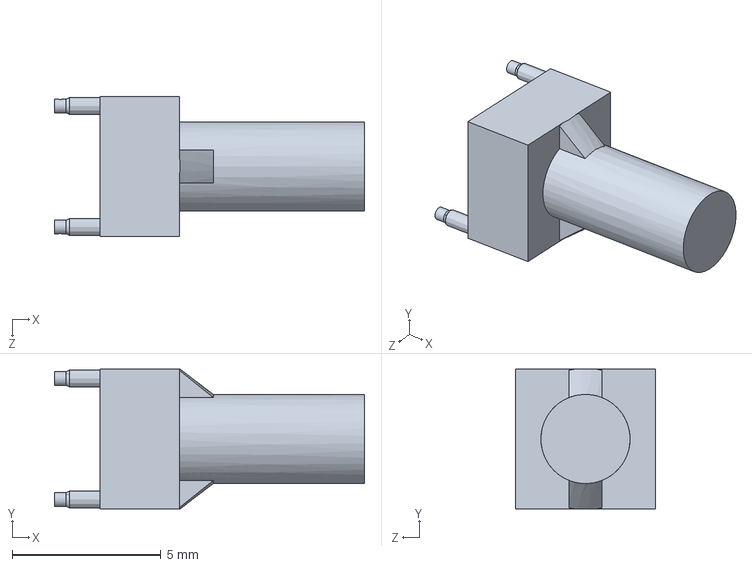
[picture p72: CAD file, 2024-07-26]
enclosure/Solidworks/VLP-350-F.SLDPRT
10.4 x 4.70 x 4.70 mm
