StonedEdge/Retro-Lite-CM5/enclosure/Solidworks/R9216.SLDPRT

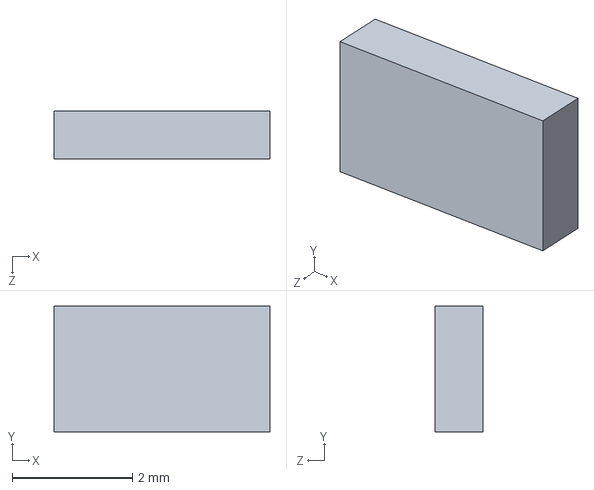
[picture p73: CAD file, 2024-07-26]
enclosure/Solidworks/R9216.SLDPRT
3.60 x 2.10 x 0.8 mm
