StonedEdge/Retro-Lite-CM5/enclosure/Solidworks/U7.SLDPRT

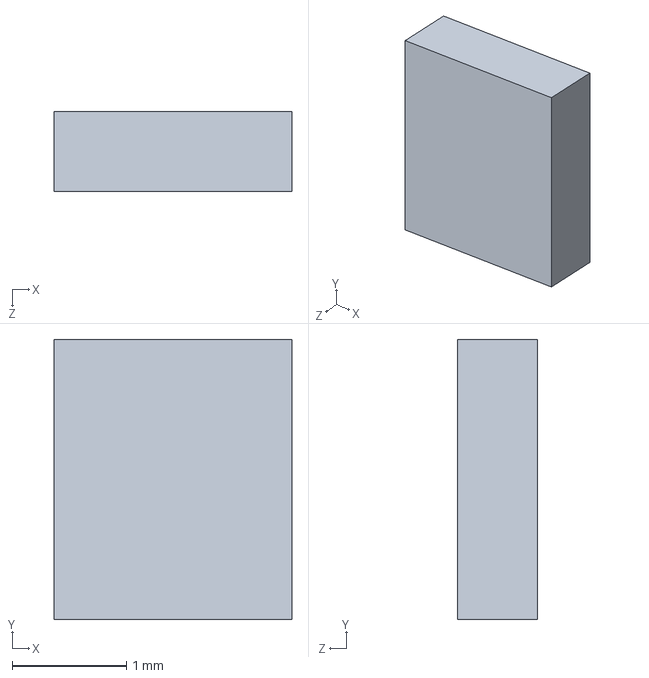
[picture p74: CAD file, 2024-07-26]
enclosure/Solidworks/U7.SLDPRT
2.08 x 2.45 x 0.7 mm
