StonedEdge/Retro-Lite-CM5/enclosure/Solidworks/U3.SLDPRT

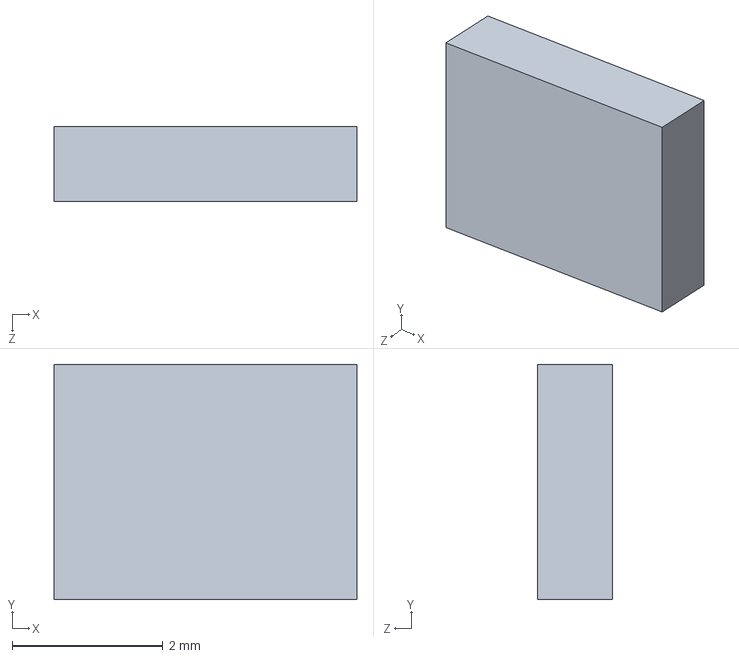
[picture p75: CAD file, 2024-07-26]
enclosure/Solidworks/U3.SLDPRT
4.03 x 3.13 x 1.00 mm
