StonedEdge/Retro-Lite-CM5/enclosure/Solidworks/U4300.SLDPRT

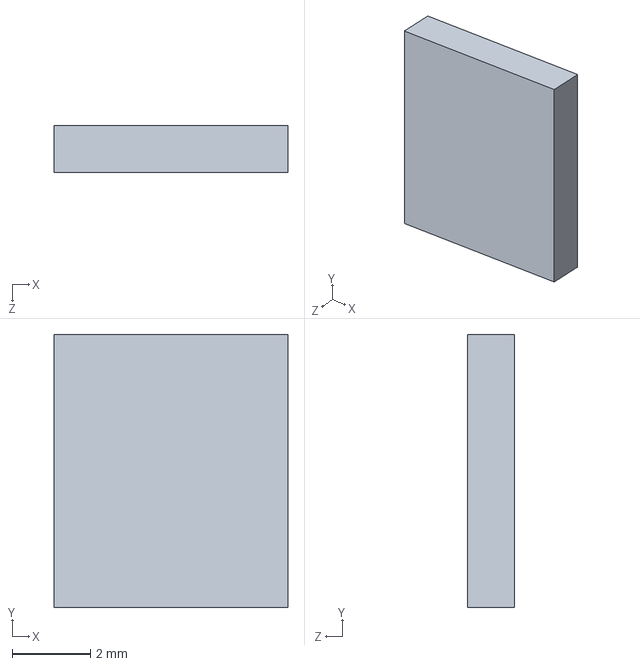
[picture p76: CAD file, 2024-07-26]
enclosure/Solidworks/U4300.SLDPRT
5.99 x 7.00 x 1.20 mm
