StonedEdge/Retro-Lite-CM5/enclosure/Solidworks/Y4.SLDPRT

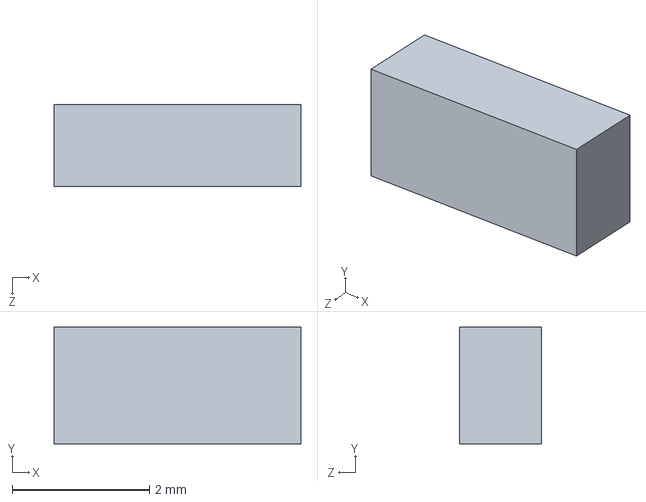
[picture p77: CAD file, 2024-07-26]
enclosure/Solidworks/Y4.SLDPRT
3.60 x 1.70 x 1.20 mm
