StonedEdge/Retro-Lite-CM5/enclosure/Solidworks/Shielding.SLDPRT

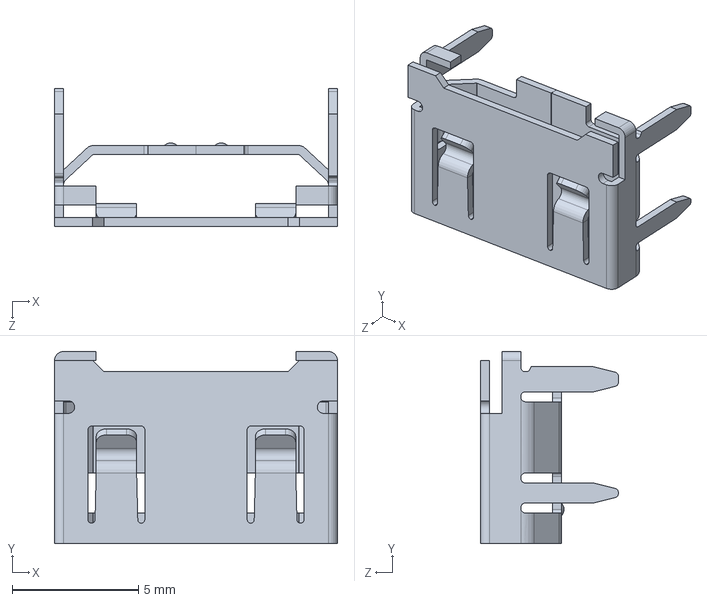
[picture p78: CAD file, 2024-07-26]
enclosure/Solidworks/Shielding.SLDPRT
11.2 x 7.60 x 5.45 mm
