StonedEdge/Retro-Lite-CM5/enclosure/Solidworks/QFN_GEFLRV_CIR v1.SLDPRT

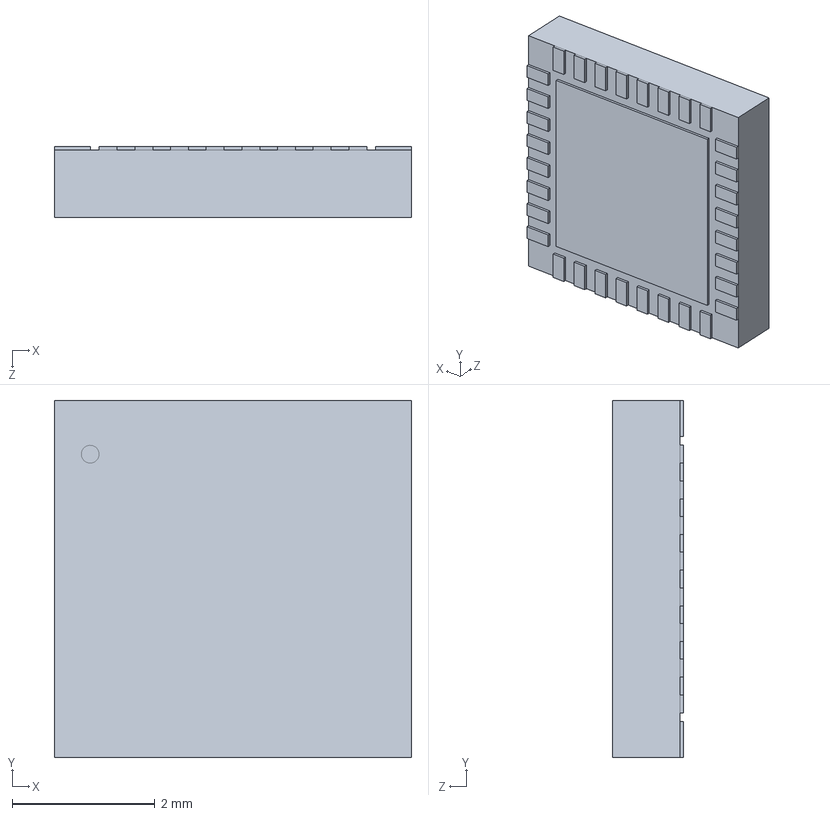
[picture p79: CAD file, 2024-07-26]
enclosure/Solidworks/QFN_GEFLRV_CIR v1.SLDPRT
5.00 x 5.00 x 0.993 mm
