StonedEdge/Retro-Lite-CM5/enclosure/Solidworks/Pin2.SLDPRT

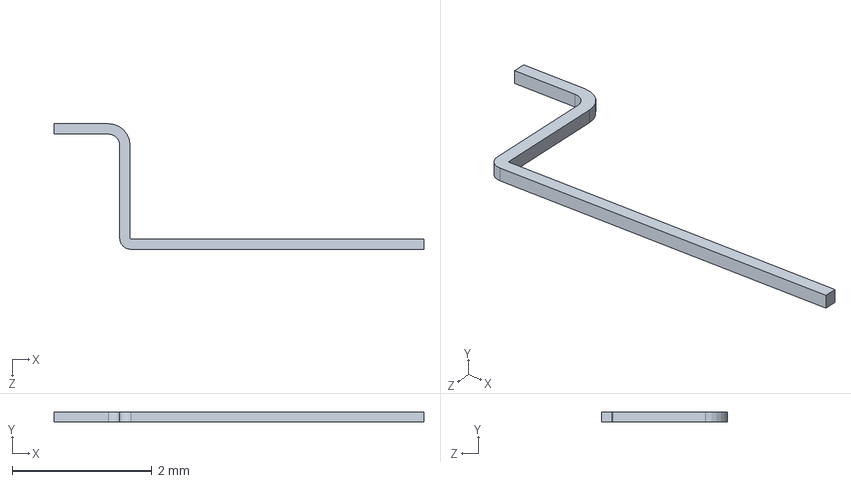
[picture p80: CAD file, 2024-07-26]
enclosure/Solidworks/Pin2.SLDPRT
5.30 x 0.15 x 1.80 mm
