StonedEdge/Retro-Lite-CM5/enclosure/Solidworks/PCIe Slot  v1.SLDPRT

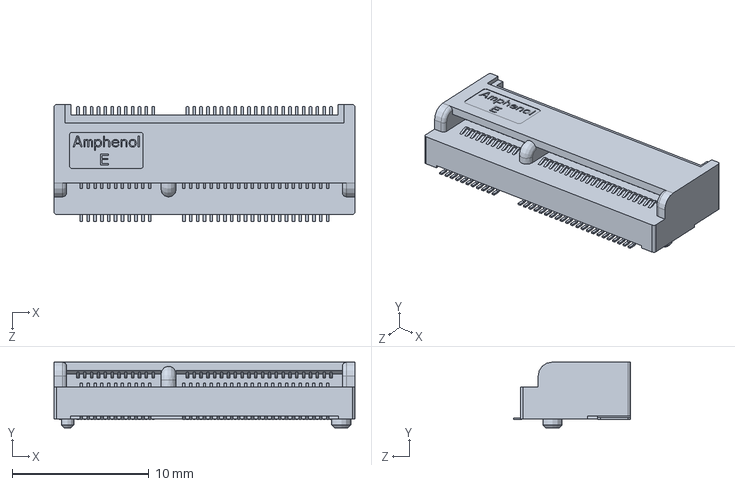
[picture p81: CAD file, 2024-07-26]
enclosure/Solidworks/PCIe Slot v1.SLDPRT
22.0 x 4.80 x 8.55 mm
