StonedEdge/Retro-Lite-CM5/enclosure/Solidworks/TP1.SLDPRT

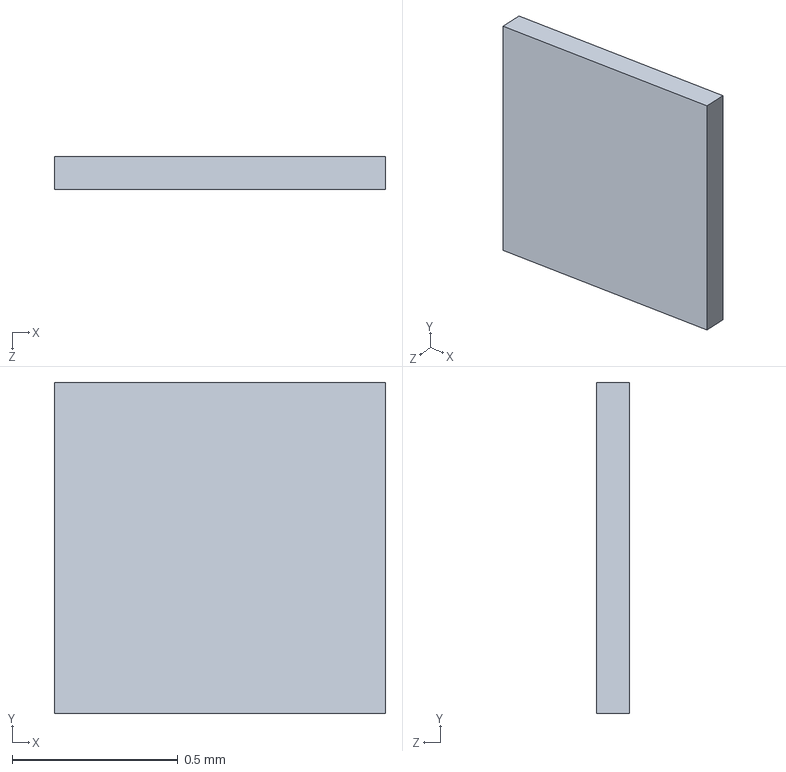
[picture p82: CAD file, 2024-07-26]
enclosure/Solidworks/TP1.SLDPRT
1.00 x 1.00 x 0.1 mm
