StonedEdge/Retro-Lite-CM5/enclosure/Solidworks/RP2040_QFN_PACKAGE v1.SLDPRT

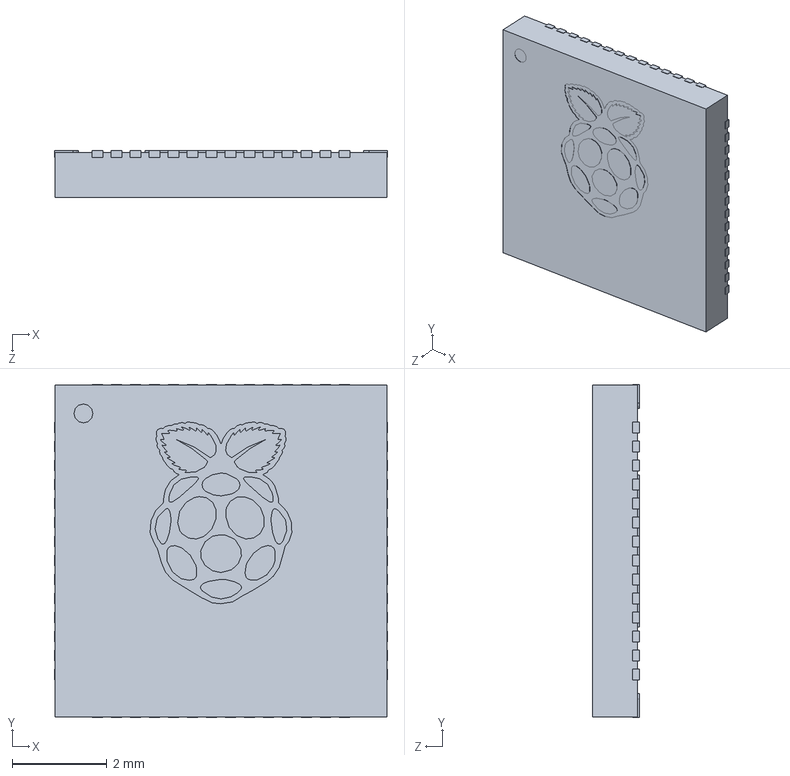
[picture p83: CAD file, 2024-07-26]
enclosure/Solidworks/RP2040_QFN_PACKAGE v1.SLDPRT
7.02 x 7.02 x 1.00 mm
