StonedEdge/Retro-Lite-CM5/enclosure/Solidworks/U2.SLDPRT

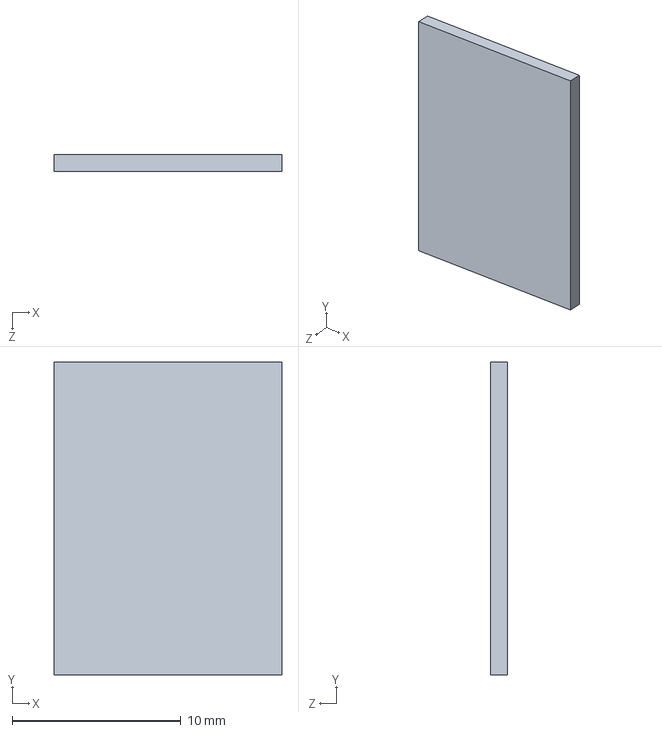
[picture p84: CAD file, 2024-07-26]
enclosure/Solidworks/U2.SLDPRT
13.5 x 18.5 x 1.00 mm
