StonedEdge/Retro-Lite-CM5/enclosure/Solidworks/Component465.SLDPRT

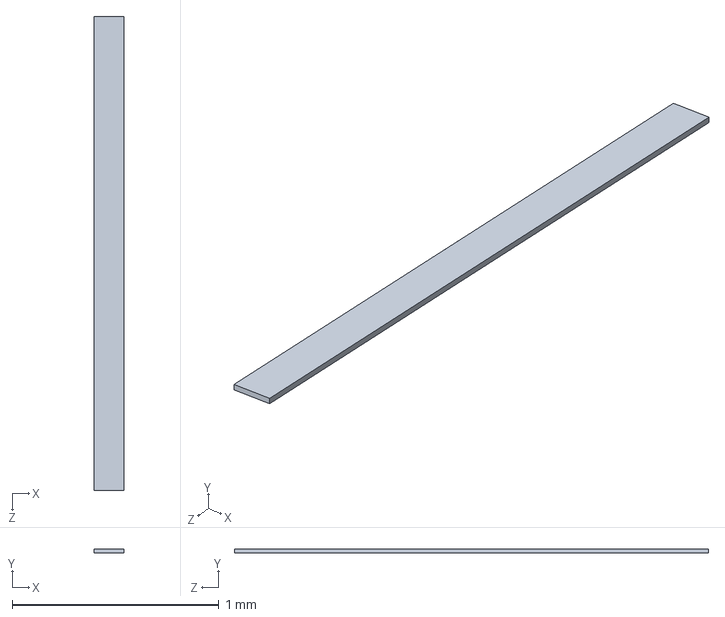
[picture p85: CAD file, 2024-07-26]
enclosure/Solidworks/Component465.SLDPRT
0.145 x 0.02 x 2.30 mm
