StonedEdge/Retro-Lite-CM5/enclosure/Solidworks/MirrorZR Trigger_1.SLDPRT

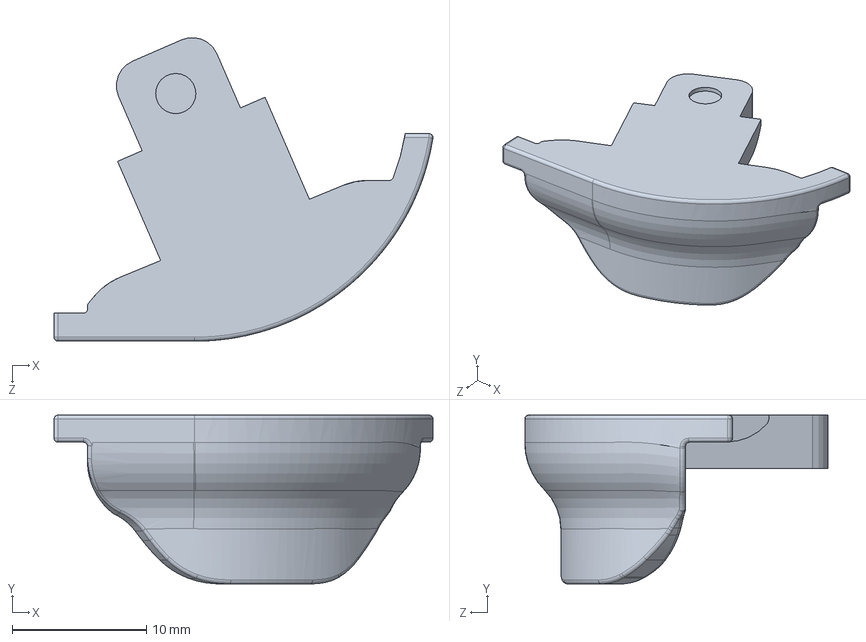
[picture p86: CAD file, 2024-07-26]
enclosure/Solidworks/MirrorZR Trigger_1.SLDPRT
28.3 x 12.6 x 22.6 mm
