StonedEdge/Retro-Lite-CM5/enclosure/Solidworks/M1.SLDPRT

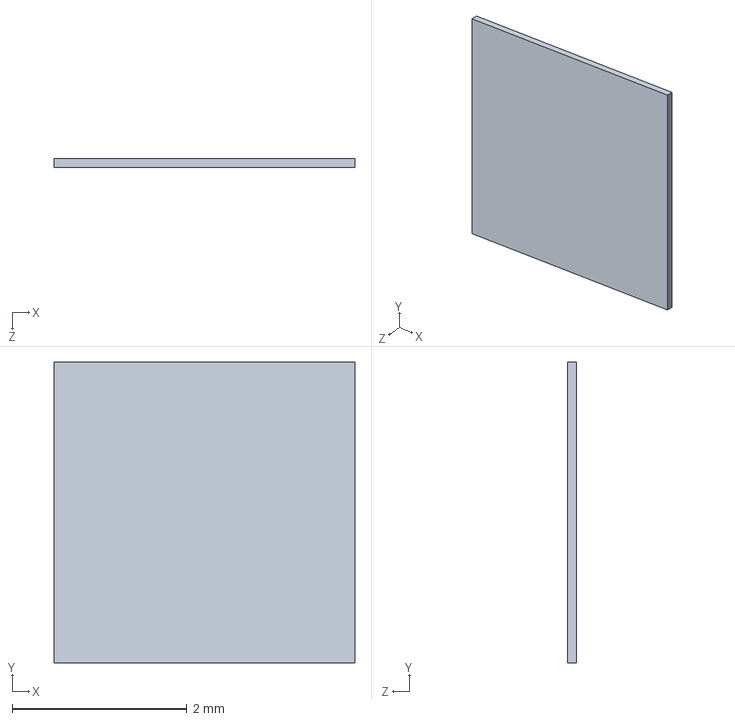
[picture p87: CAD file, 2024-07-26]
enclosure/Solidworks/M1.SLDPRT
3.45 x 3.45 x 0.1 mm
