StonedEdge/Retro-Lite-CM5/enclosure/Solidworks/Housing.SLDPRT

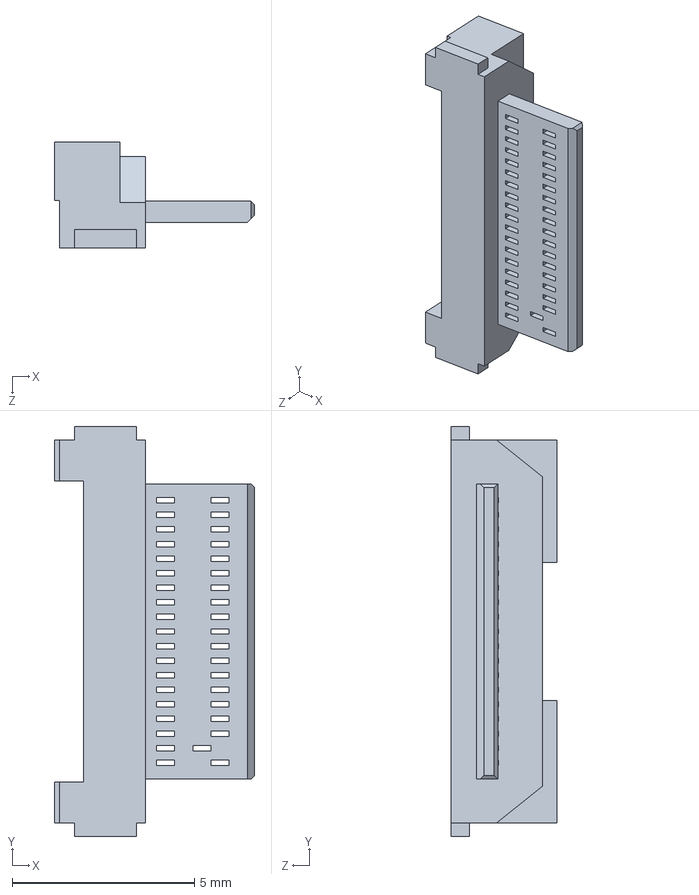
[picture p88: CAD file, 2024-07-26]
enclosure/Solidworks/Housing.SLDPRT
5.50 x 11.2 x 2.90 mm
