StonedEdge/Retro-Lite-CM5/enclosure/Solidworks/Housing2.SLDPRT

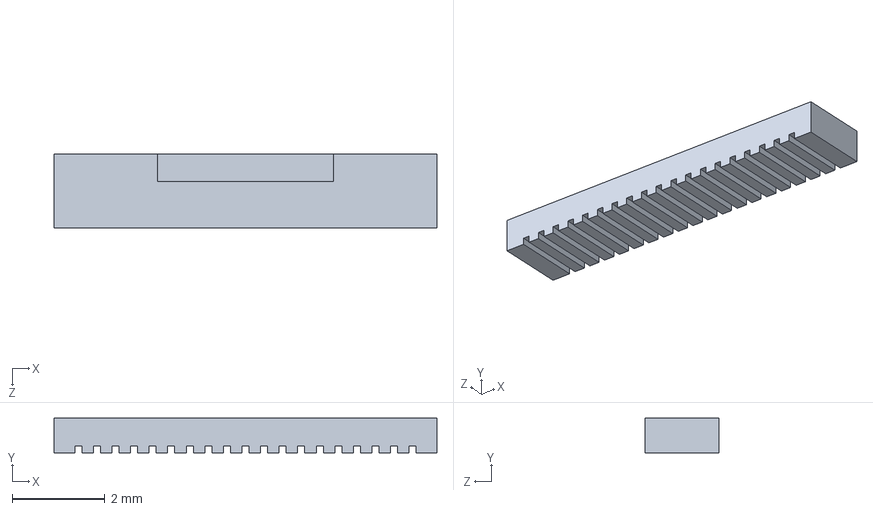
[picture p89: CAD file, 2024-07-26]
enclosure/Solidworks/Housing2.SLDPRT
8.25 x 0.75 x 1.60 mm
