StonedEdge/Retro-Lite-CM5/enclosure/Solidworks/LED1.SLDPRT

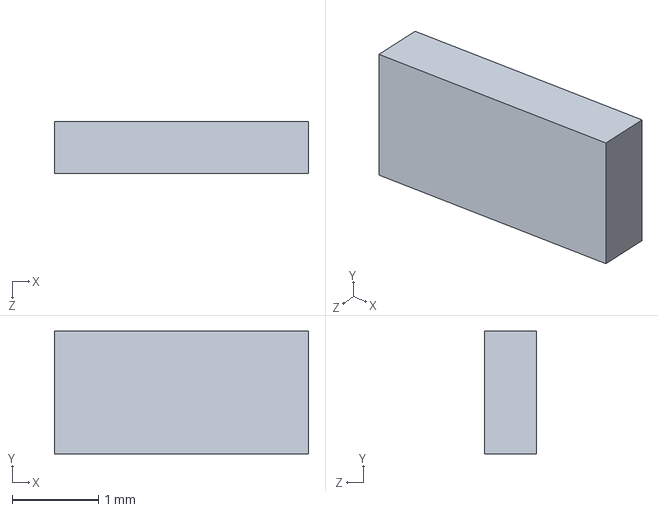
[picture p90: CAD file, 2024-07-26]
enclosure/Solidworks/LED1.SLDPRT
2.95 x 1.43 x 0.6 mm
