StonedEdge/Retro-Lite-CM5/enclosure/Solidworks/FB9.SLDPRT

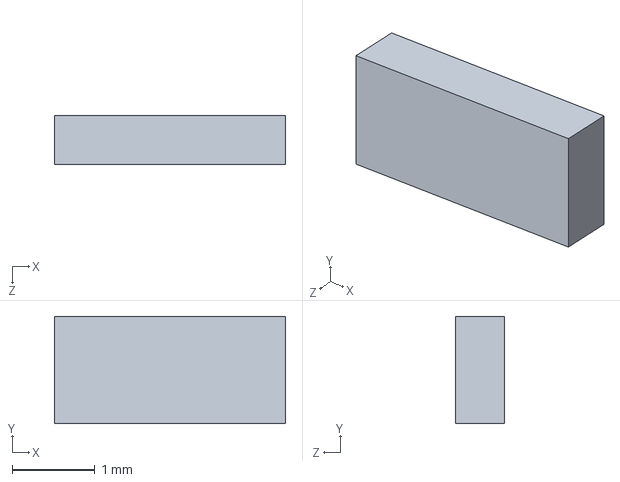
[picture p91: CAD file, 2024-07-26]
enclosure/Solidworks/FB9.SLDPRT
2.80 x 1.30 x 0.6 mm
