StonedEdge/Retro-Lite-CM5/enclosure/Solidworks/L10.SLDPRT

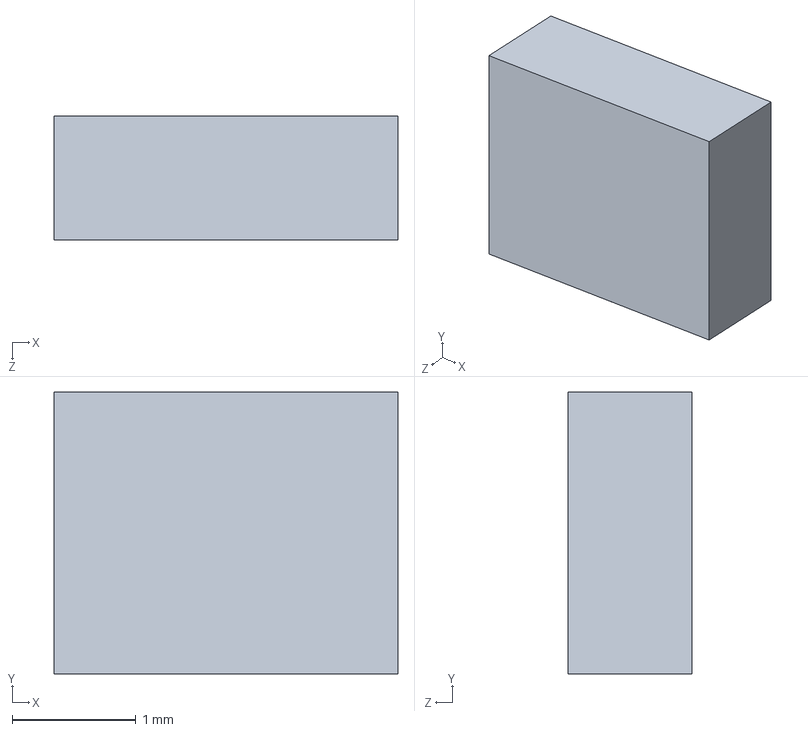
[picture p92: CAD file, 2024-07-26]
enclosure/Solidworks/L10.SLDPRT
2.78 x 2.28 x 1.00 mm
