StonedEdge/Retro-Lite-CM5/enclosure/Solidworks/L2.SLDPRT

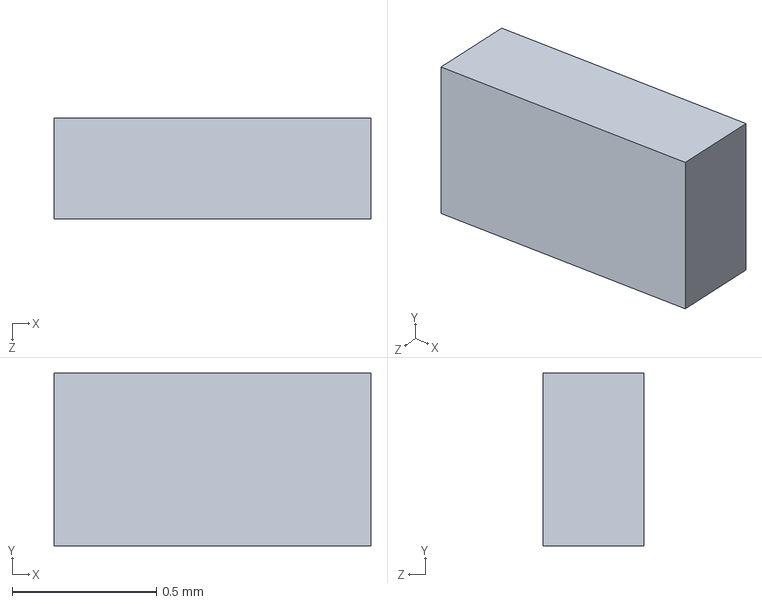
[picture p93: CAD file, 2024-07-26]
enclosure/Solidworks/L2.SLDPRT
1.10 x 0.6 x 0.35 mm
