StonedEdge/Retro-Lite-CM5/enclosure/Solidworks/DF40C-100DS.SLDPRT

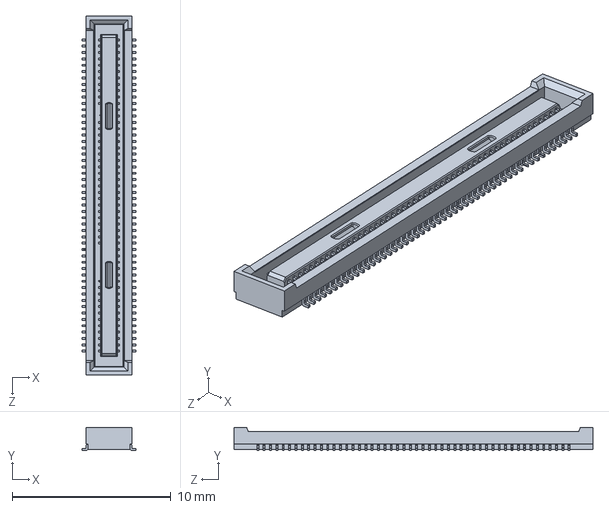
[picture p94: CAD file, 2024-07-26]
enclosure/Solidworks/DF40C-100DS.SLDPRT
3.38 x 1.45 x 22.6 mm
