StonedEdge/Retro-Lite-CM5/enclosure/Solidworks/FB5.SLDPRT

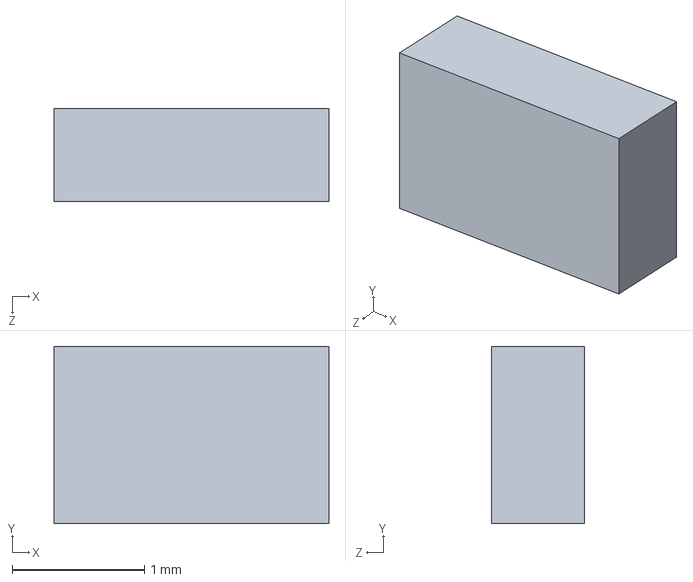
[picture p95: CAD file, 2024-07-26]
enclosure/Solidworks/FB5.SLDPRT
2.08 x 1.34 x 0.7 mm
