StonedEdge/Retro-Lite-CM5/enclosure/Solidworks/D1.SLDPRT

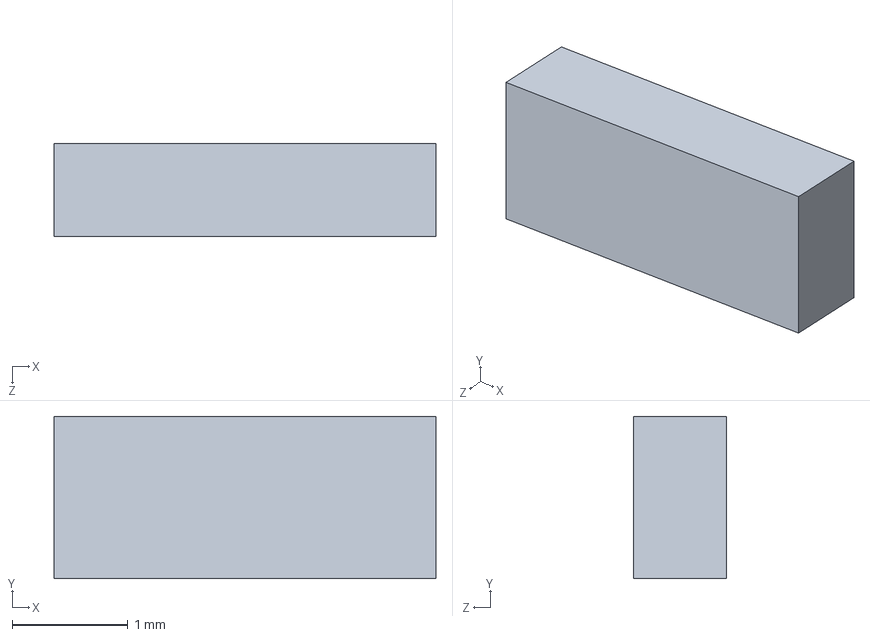
[picture p96: CAD file, 2024-07-26]
enclosure/Solidworks/D1.SLDPRT
3.30 x 1.40 x 0.8 mm
