StonedEdge/Retro-Lite-CM5/enclosure/Solidworks/Micro SD-Card.SLDPRT

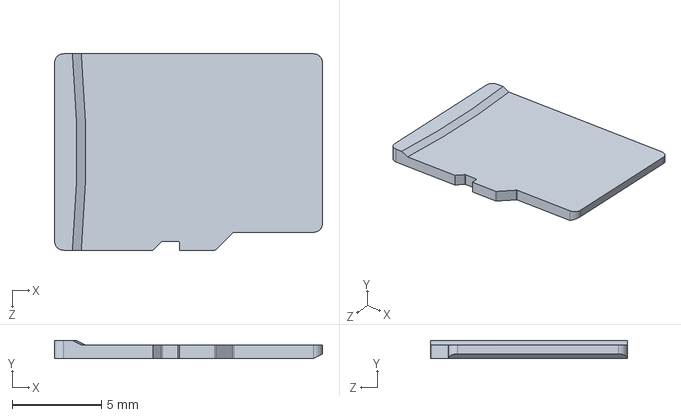
[picture p97: CAD file, 2024-07-26]
enclosure/Solidworks/Micro SD-Card.SLDPRT
15.0 x 1.01 x 11.0 mm
