StonedEdge/Retro-Lite-CM5/rp2040_gamepad/src/gamepad.cpp

#include "gamepad.h"
#include "hardware/adc.h"
#include "hardware/flash.h"
#include "pico/stdlib.h"
#include "pico/bootrom.h"
#include <algorithm>

#define PIN_A 0
#define PIN_B 1
#define PIN_X 2
#define PIN_Y 25
#define PIN_START 16
#define PIN_SELECT 11
#define PIN_D_UP 12
#define PIN_D_DOWN 13
#define PIN_D_LEFT 14
#define PIN_D_RIGHT 15
#define PIN_L2_HALF 20
#define PIN_R2_HALF 8
#define PIN_L2_FULL 21
#define PIN_R2_FULL 7
#define PIN_R1 9
#define PIN_L1 10
#define PIN_L3 23
#define PIN_R3 3
#define PIN_HOTKEY_MINUS 17
#define PIN_HOTKEY_PLUS 24

// Array to store digital pins used for buttons.
uint8_t buttonPins[buttonCount] = {
    PIN_A, PIN_B, PIN_X, PIN_Y, PIN_START, PIN_SELECT, PIN_L2_HALF, PIN_R2_HALF, PIN_L2_FULL,
    PIN_R2_FULL, PIN_R1, PIN_L1, PIN_L3, PIN_R3, PIN_HOTKEY_MINUS, PIN_HOTKEY_PLUS
};

// Up, Right, Down, Left. Do not change order of directions.
uint8_t dpadPins[4] = { PIN_D_UP, PIN_D_RIGHT, PIN_D_DOWN, PIN_D_LEFT };

// Button state arrays
bool dpadPinState[4];
bool buttonState[buttonCount];

const int joystickPins[4] = { 26, 27, 28, 29 };

// Joystick Settings
// Change these settings for Inverted mounting of joysticks.
bool invertOutput[4] = { true, true, false, false };

// Joystick deadband settings. Deadband is the same for both axis on each joystick.
int axisDeadband[4] = { 64, 64, 64, 64 };

// Distance from end of travel to achieve full axis movement.
// This helps square out each axis response to allow full movement speed with direction input.
int axisEarly[4] = { 120, 120, 120, 120 };

int axisMin[4] = { 0, 0, 0, 0 };
int axisMid[4] = { 2048, 2048, 2048, 2048 };
int axisMax[4] = { 4095, 4095, 4095, 4095 };

// All variables below general use, not used for configuration.
bool calibrationMode = false;
int calibrationStep = 1;

Toggle menuEnabled;
Toggle povHatMode(true); // Enable to use POV Hat for Dpad instead of analog

hid_gamepad_report_t joystick;
hid_gamepad_report_t lastState;

static inline long map(long x, long in_min, long in_max, long out_min, long out_max)
{
    return (x - in_min) * (out_max - out_min) / (in_max - in_min) + out_min;
}

uint8_t axisMap(int i, int minIn, int midIn, int maxIn, int earlyStop, int deadBand)
{
    // Shift all joystick values to a base of zero.
    int shiftedMin = 0;
    int shiftedMid = midIn - minIn;
    int shiftedMax = maxIn - minIn;

    if (i < shiftedMid + deadBand && i > shiftedMid - deadBand)
        return 0;
    if (i < shiftedMid) {
        if (i > shiftedMin + earlyStop)
            return map(i, shiftedMin, shiftedMid - deadBand, -127, 0);
        return -127;
    }
    if (i < shiftedMax - earlyStop)
        return map(i, shiftedMid + deadBand, shiftedMax, 0, 127);
    return 127;
}

int readJoystick(int joystickAxis)
{ // Reads raw joystick values and inverts if required
    adc_select_input(joystickAxis);
    return invertOutput[joystickAxis] ? 4095 - adc_read() : adc_read();
}

int8_t mapJoystick(int axis)
{
    int var = readJoystick(axis) - axisMin[axis];
    return axisMap(
        var, axisMin[axis], axisMid[axis], axisMax[axis], axisEarly[axis], axisDeadband[axis]);
}

void buttonRead()
{ // Read button inputs and set state arrays.
    for (int i = 0; i < buttonCount; i++)
        buttonState[i] = !gpio_get(buttonPins[i]);

    for (int i = 0; i < 4; i++)
        dpadPinState[i] = !gpio_get(dpadPins[i]);
}

void joypadButtons()
{ // Set joystick buttons for USB output
    uint32_t buttons = 0;
    for (int i = 0; i < buttonCount; i++)
        buttons |= ((uint32_t)buttonState[i] << i);
    joystick.buttons = buttons;
}

bool checkButtons()
{
    for (int i = 0; i < buttonCount; i++)
        if (!gpio_get(buttonPins[i]))
            return true;
    return false;
}

void dPadInput()
{ // D-Pad as RY and RZ Axis
    if (!povHatMode) {
        if (dpadPinState[DPAD_UP])
            joystick.ry = 127;
        else if (dpadPinState[DPAD_DOWN])
            joystick.ry = -127;
        else
            joystick.ry = 0;

        if (dpadPinState[DPAD_RIGHT])
            joystick.rz = 127;
        else if (dpadPinState[DPAD_LEFT])
            joystick.rz = -127;
        else
            joystick.rz = 0;
    } else { // POV Hat Mode
        joystick.hat = GAMEPAD_HAT_CENTERED;
        if (dpadPinState[DPAD_UP]) {
            if (dpadPinState[DPAD_RIGHT])
                joystick.hat = GAMEPAD_HAT_UP_RIGHT;
            else if (dpadPinState[DPAD_LEFT])
                joystick.hat = GAMEPAD_HAT_UP_LEFT;
            else
                joystick.hat = GAMEPAD_HAT_UP;
        } else if (dpadPinState[DPAD_DOWN]) {
            if (dpadPinState[DPAD_RIGHT])
                joystick.hat = GAMEPAD_HAT_DOWN_RIGHT;
            else if (dpadPinState[DPAD_LEFT])
                joystick.hat = GAMEPAD_HAT_DOWN_LEFT;
            else
                joystick.hat = GAMEPAD_HAT_DOWN;
        } else if (dpadPinState[DPAD_RIGHT])
            joystick.hat = GAMEPAD_HAT_RIGHT;
        else if (dpadPinState[DPAD_LEFT])
            joystick.hat = GAMEPAD_HAT_LEFT;
    }
}

#define FLASH_TARGET_OFFSET (4 * 1024 * 1024)
#define FLASH_MAGIC (int)0xFFFFBEEF

const uint8_t* flash_target_contents = (const uint8_t*)(XIP_BASE + FLASH_TARGET_OFFSET);

int flashOffset = -1;

uint8_t flashData[FLASH_PAGE_SIZE];

void writeIntIntoFlash(int number)
{ // Splits Int into uint8_tS for Flash
    uint8_t byte1 = number >> 8;
    uint8_t byte2 = number & 0xFF;
    flashData[flashOffset] = byte1;
    flashData[flashOffset + 1] = byte2;
    flashOffset += 2;
}

int readIntFromFlash()
{ // Converts uint8_tS to INT from Flash
    uint8_t byte1 = flash_target_contents[flashOffset];
    uint8_t byte2 = flash_target_contents[flashOffset + 1];
    flashOffset += 2;
    return (int16_t)((byte1 << 8) + byte2);
}

void readJoystickConfig()
{ // Read joystick calibration from Flash
    flashOffset = 0;
    if (readIntFromFlash() != FLASH_MAGIC) // Check Joystick Calibration in Flash is not Empty
        return;

    for (int i = 0; i < 4; i++) {
        axisMin[i] = readIntFromFlash();
        axisMid[i] = readIntFromFlash();
        axisMax[i] = readIntFromFlash();
    }

    // IMU calibration data
    xAccelOffset = readIntFromFlash();
    yAccelOffset = readIntFromFlash();
    zAccelOffset = readIntFromFlash();
    xGyroOffset = readIntFromFlash();
    yGyroOffset = readIntFromFlash();
    zGyroOffset = readIntFromFlash();
}

void writeJoystickConfig()
{ // Store joystick calibration in Flash
    flash_range_erase(FLASH_TARGET_OFFSET, FLASH_SECTOR_SIZE);

    flashOffset = 0;
    writeIntIntoFlash(FLASH_MAGIC);

    for (int i = 0; i < 4; i++) {
        writeIntIntoFlash(axisMin[i]);
        writeIntIntoFlash(axisMid[i]);
        writeIntIntoFlash(axisMax[i]);
    }

    // IMU calibration data
    writeIntIntoFlash(xAccelOffset);
    writeIntIntoFlash(yAccelOffset);
    writeIntIntoFlash(zAccelOffset);
    writeIntIntoFlash(xGyroOffset);
    writeIntIntoFlash(yGyroOffset);
    writeIntIntoFlash(zGyroOffset);

    flash_range_program(FLASH_TARGET_OFFSET, flashData, FLASH_PAGE_SIZE);
}

void joystickCalibration()
{ // Very rough at the moment but it works.
    if (calibrationStep == 1) {
        if (buttonState[BTN_A]) // Wait for button press
            calibrationStep = 2;
    } else if (calibrationStep == 2) {
        if (!buttonState[BTN_A]) { // Wait for button release and read the center values
            for (int i = 0; i < 4; i++) {
                axisMid[i] = readJoystick(i);
                axisMin[i] = axisMid[i];
                axisMax[i] = 0;
            }
            tud_cdc_write_char(calibrationStepTwo);
            calibrationStep = 3;
        }
    } else if (calibrationStep == 3) {
        for (int i = 0; i < 4; i++) {
            int var = readJoystick(i);
            axisMin[i] = std::min(axisMin[i], var);
            axisMax[i] = std::max(axisMax[i], var);
        }
        if (buttonState[BTN_A]) { // Complete Calibration
            writeJoystickConfig(); // Update Flash
            tud_cdc_write_char(calibrationComplete);
            calibrationStep = 1;
            calibrationMode = false;
        }
    }
}

void joystickInput()
{
    joystick.rx = mapJoystick(JOY_RIGHT_Y);
    joystick.z = mapJoystick(JOY_RIGHT_X);
    joystick.y = mapJoystick(JOY_LEFT_Y);
    joystick.x = mapJoystick(JOY_LEFT_X);
}

void pinModeInputPullup(int pin)
{
    gpio_init(pin);
    gpio_set_dir(pin, GPIO_IN);
    gpio_pull_up(pin);
}

void gamepad_init()
{
    memset(&joystick, 0, sizeof(joystick));
    memset(&lastState, 0, sizeof(lastState));

    // Set all button pins as input pullup. Change to INPUT if using external resistors.
    for (int i = 0; i < buttonCount; i++)
        pinModeInputPullup(buttonPins[i]);

    for (int i = 0; i < 4; i++) // Set all dpad button pins as input pullup.
        pinModeInputPullup(dpadPins[i]);

    adc_init();
    for (int i = 0; i < 4; i++)
        adc_gpio_init(joystickPins[i]);

    readJoystickConfig(); // Check for stored joystick settings and load if applicable.
}

uint16_t get_gamepad_report(uint8_t* buffer, uint16_t reqlen)
{
    if (reqlen >= sizeof(joystick)) {
        memcpy(buffer, &joystick, sizeof(joystick));
        return sizeof(joystick);
    }

    return 0;
}

bool send_gamepad_report()
{
    // Poll every 5ms
    const uint32_t interval_ms = 5;
    static uint32_t start_ms = 0;

    if (board_millis() - start_ms < interval_ms)
        return false; // not enough time
    start_ms += interval_ms;

    buttonRead();

    if (calibrationMode)
        joystickCalibration();
    else if (!menuEnabled) {
        joypadButtons();
        joystickInput();
        dPadInput();

        // Hotkey+ and R3 for jostick calibration
        if (buttonState[BTN_HOTKEY_PLUS] && buttonState[BTN_R3]) {
            calibrationStep = 1;
            calibrationMode = true;
        }
        else if (buttonState[BTN_HOTKEY_PLUS] && buttonState[BTN_HOTKEY_MINUS]
                && buttonState[BTN_SELECT] && buttonState[BTN_START]) {
            // Ctrl+Alt+Del
            reset_usb_boot(0, 0);
        }
        else if (memcmp(&lastState, &joystick, sizeof(joystick)) && !buttonState[BTN_HOTKEY_PLUS]) {
            tud_hid_report(REPORT_ID_GAMEPAD, &joystick, sizeof(joystick));
            lastState = joystick;
            return true;
        }
    }

    return false;
}
